JoeyStrandnes/TSTE93_Slutsteget/Documentation/Freq_Respons/html/Smooth_01.png

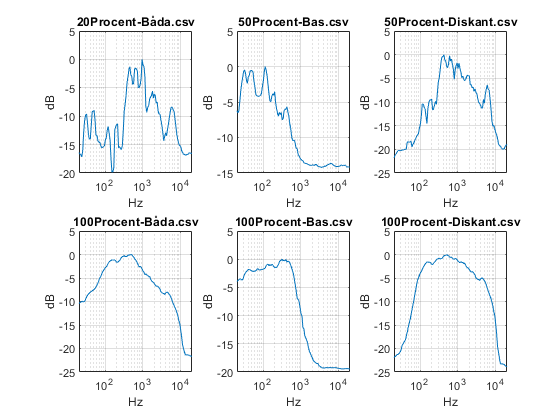
Documentation/Freq_Respons/html/Smooth_01.png
