JoeyStrandnes/TSTE93_Slutsteget/Documentation/Freq_Respons/html/Smooth_02.png

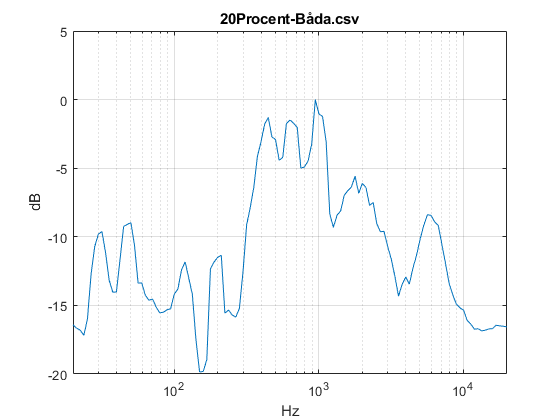
Documentation/Freq_Respons/html/Smooth_02.png
