JoeyStrandnes/TSTE93_Slutsteget/Documentation/Freq_Respons/html/Smooth_03.png

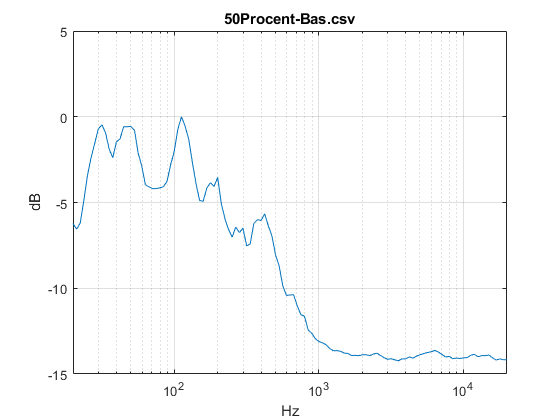
Documentation/Freq_Respons/html/Smooth_03.png
