JoeyStrandnes/TSTE93_Slutsteget/Documentation/Freq_Respons/html/Smooth_04.png

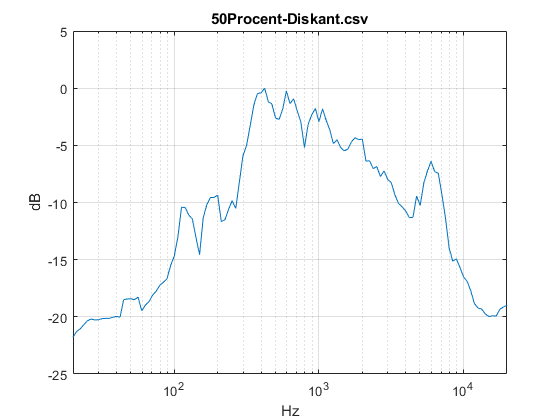
Documentation/Freq_Respons/html/Smooth_04.png
