JoeyStrandnes/TSTE93_Slutsteget/Documentation/Freq_Respons/html/Smooth_05.png

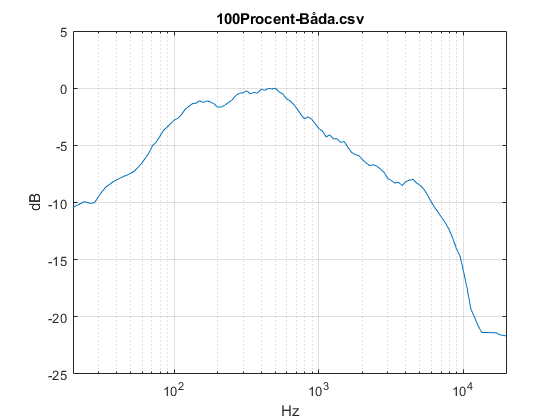
Documentation/Freq_Respons/html/Smooth_05.png
