JoeyStrandnes/TSTE93_Slutsteget/Documentation/Freq_Respons/html/Smooth_06.png

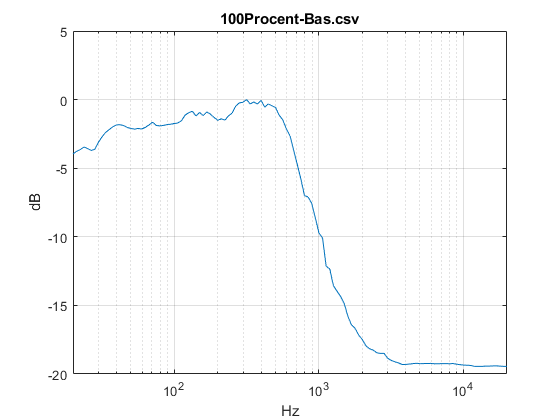
Documentation/Freq_Respons/html/Smooth_06.png
