JoeyStrandnes/TSTE93_Slutsteget/Documentation/Freq_Respons/html/Smooth_07.png

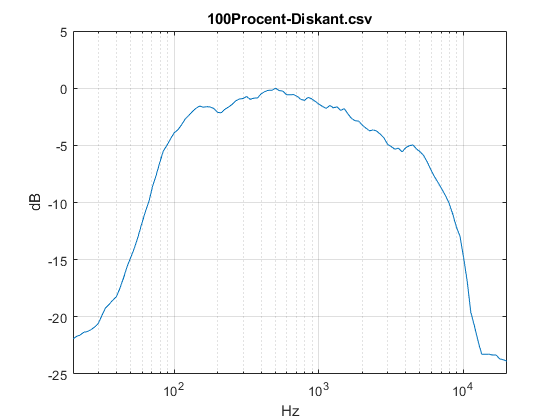
Documentation/Freq_Respons/html/Smooth_07.png
