JoeyStrandnes/TSTE93_Slutsteget/Documentation/Images/DAC-Output.png

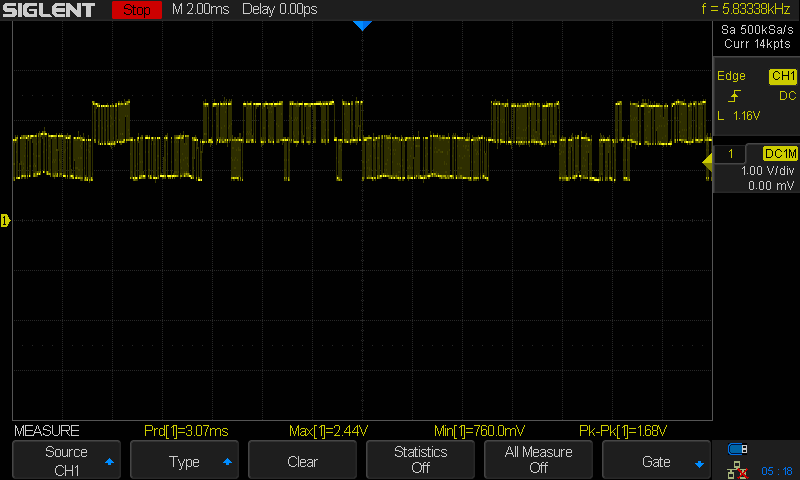
Documentation/Images/DAC-Output.png
