JoeyStrandnes/TSTE93_Slutsteget/Documentation/Images/Misc/20210310_001052.jpg

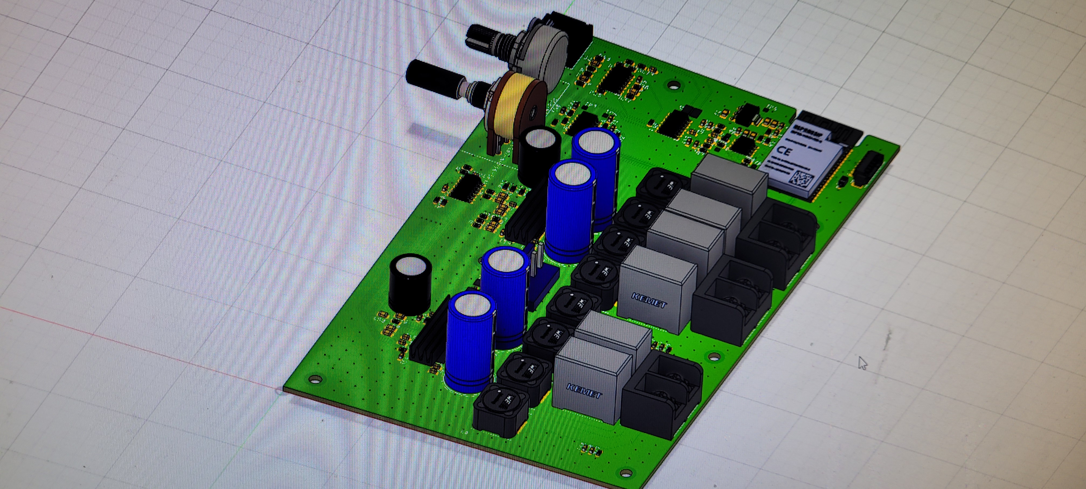
Documentation/Images/Misc/20210310_001052.jpg
