JoeyStrandnes/TSTE93_Slutsteget/Documentation/Images/Misc/20210327_163234.jpg

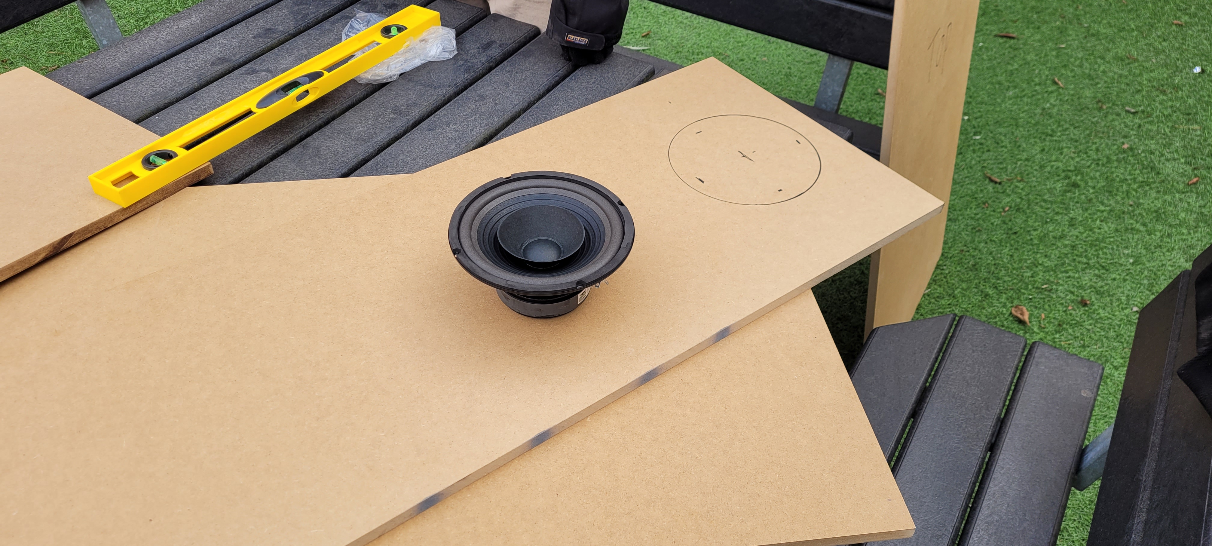
Documentation/Images/Misc/20210327_163234.jpg
