JoeyStrandnes/TSTE93_Slutsteget/Documentation/Images/Misc/20210327_163858.jpg

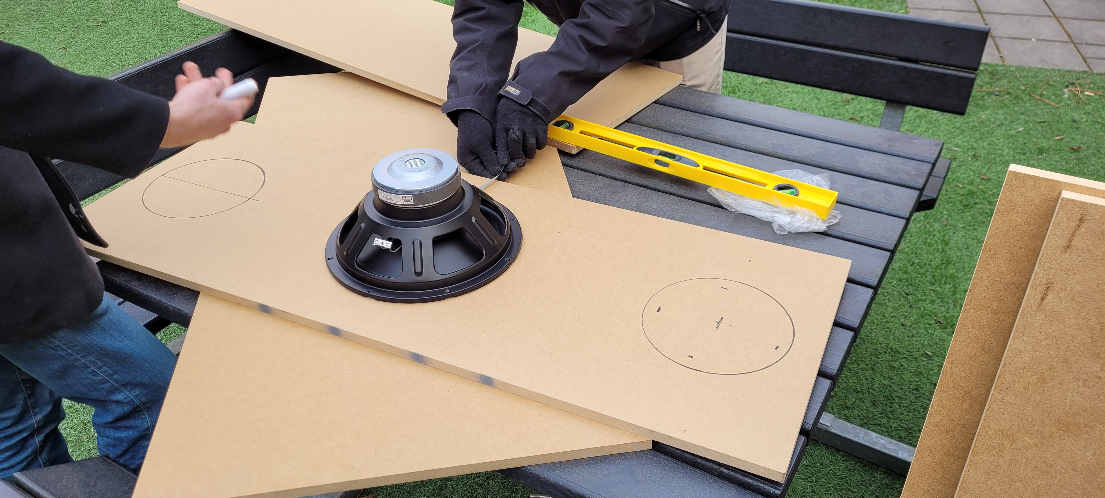
Documentation/Images/Misc/20210327_163858.jpg
