JoeyStrandnes/TSTE93_Slutsteget/Documentation/Images/Misc/20210327_181533.jpg

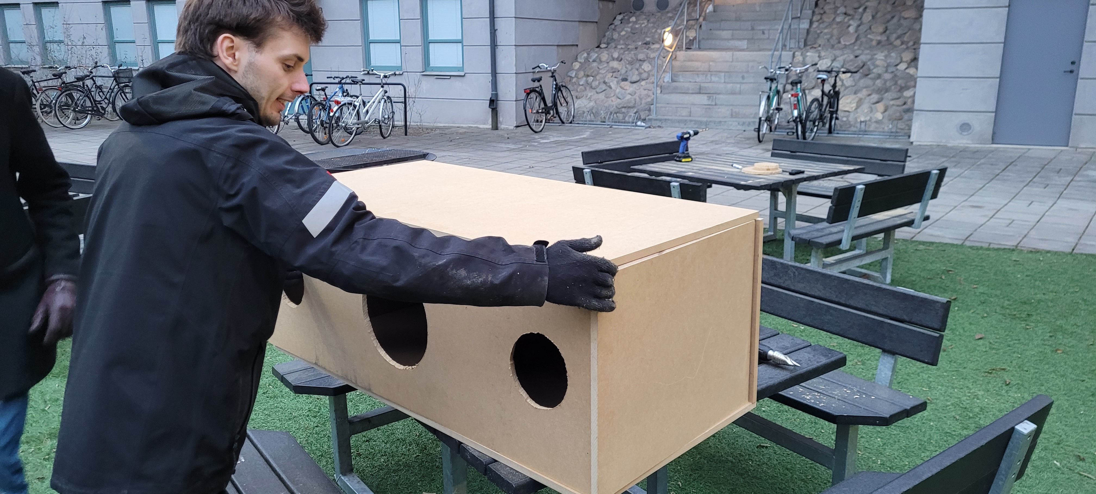
Documentation/Images/Misc/20210327_181533.jpg
