JoeyStrandnes/TSTE93_Slutsteget/Documentation/Images/Misc/20210327_181544.jpg

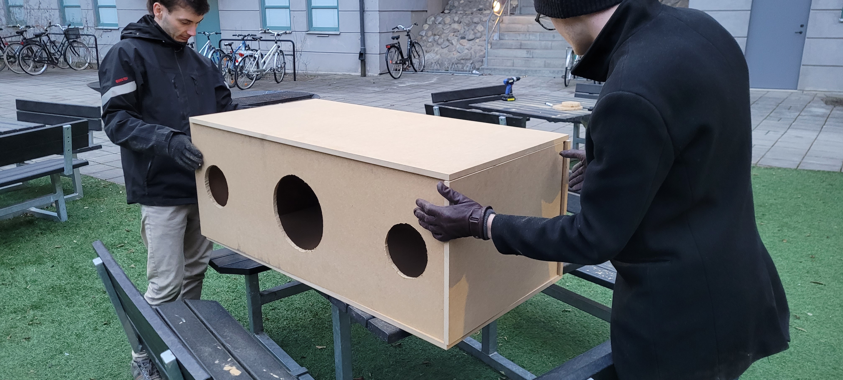
Documentation/Images/Misc/20210327_181544.jpg
