JoeyStrandnes/TSTE93_Slutsteget/Documentation/Images/Misc/20210410_160741.jpg

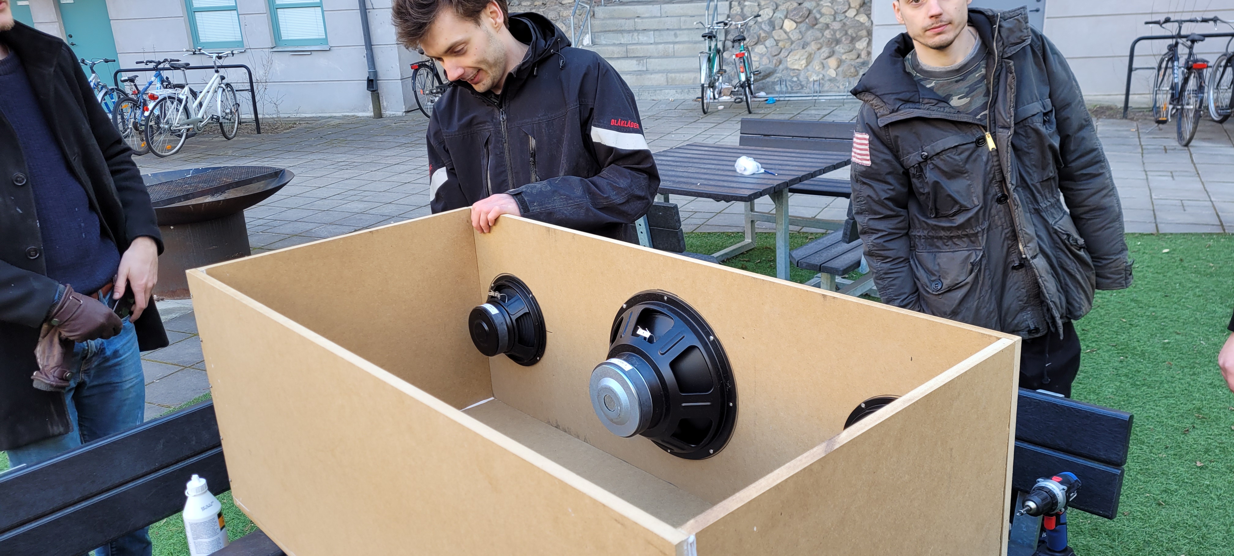
Documentation/Images/Misc/20210410_160741.jpg
