JoeyStrandnes/TSTE93_Slutsteget/Documentation/Images/Misc/20210410_160745.jpg

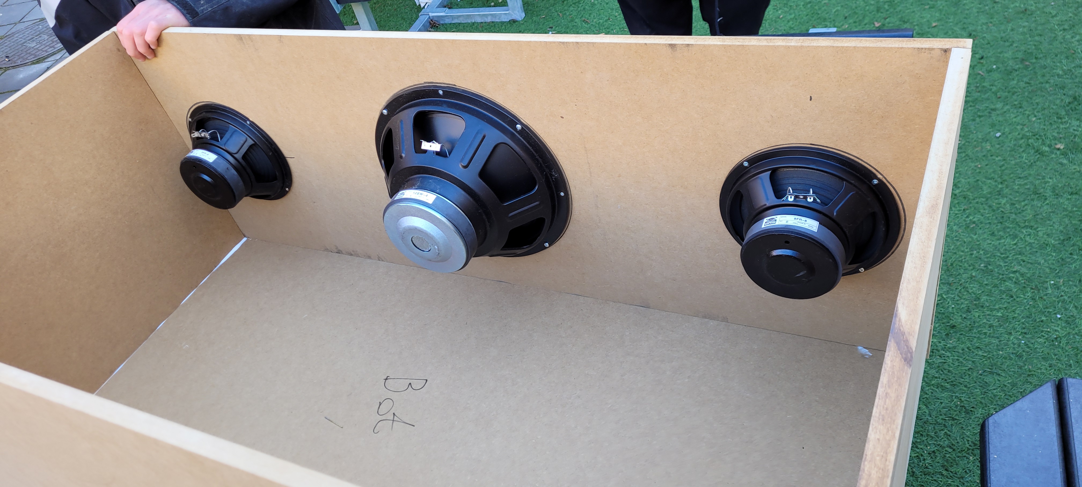
Documentation/Images/Misc/20210410_160745.jpg
