JoeyStrandnes/TSTE93_Slutsteget/Documentation/Images/Misc/20210410_163332.jpg

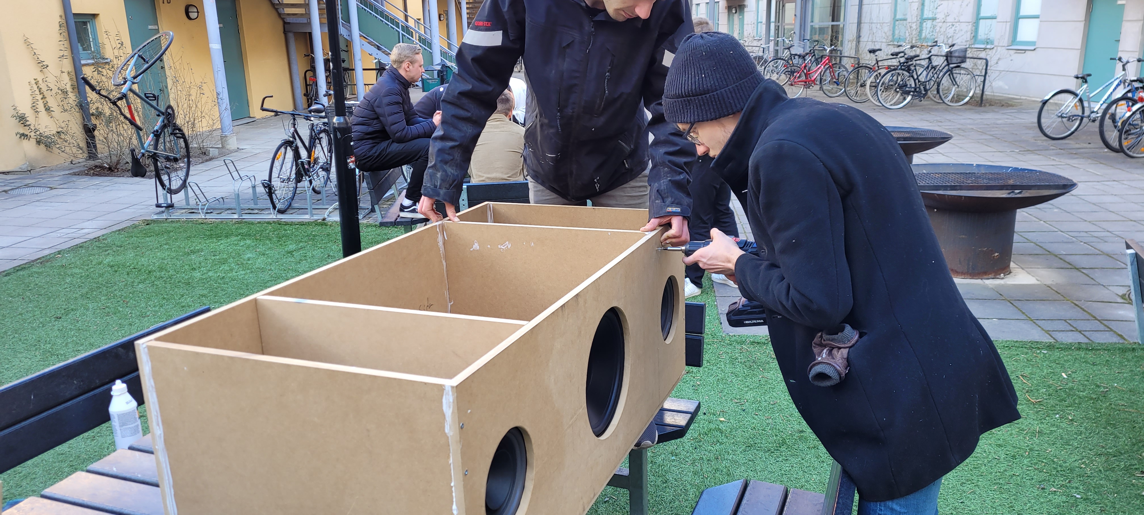
Documentation/Images/Misc/20210410_163332.jpg
