JoeyStrandnes/TSTE93_Slutsteget/Documentation/Images/Misc/20210410_163335.jpg

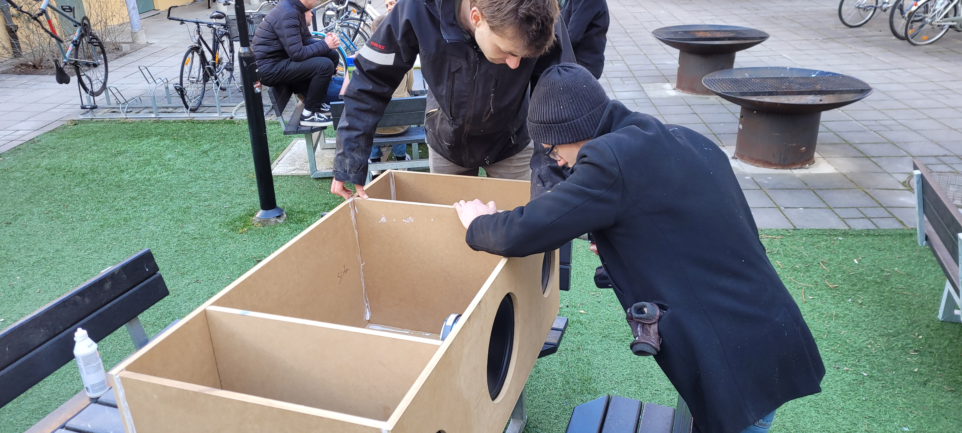
Documentation/Images/Misc/20210410_163335.jpg
