JoeyStrandnes/TSTE93_Slutsteget/Documentation/Images/Misc/20210410_163340.jpg

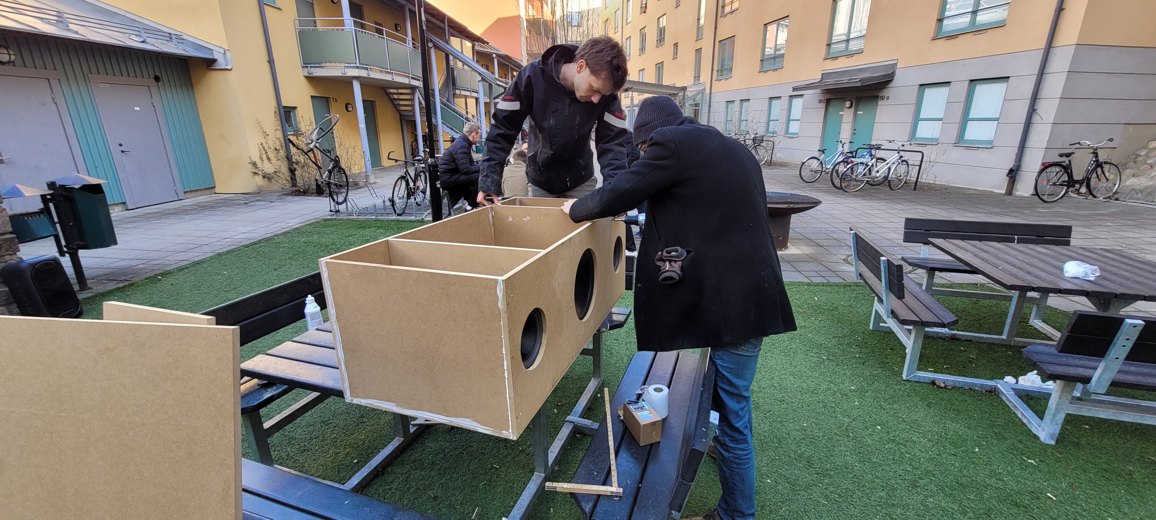
Documentation/Images/Misc/20210410_163340.jpg
