JoeyStrandnes/TSTE93_Slutsteget/Documentation/Images/Misc/20210410_170837.jpg

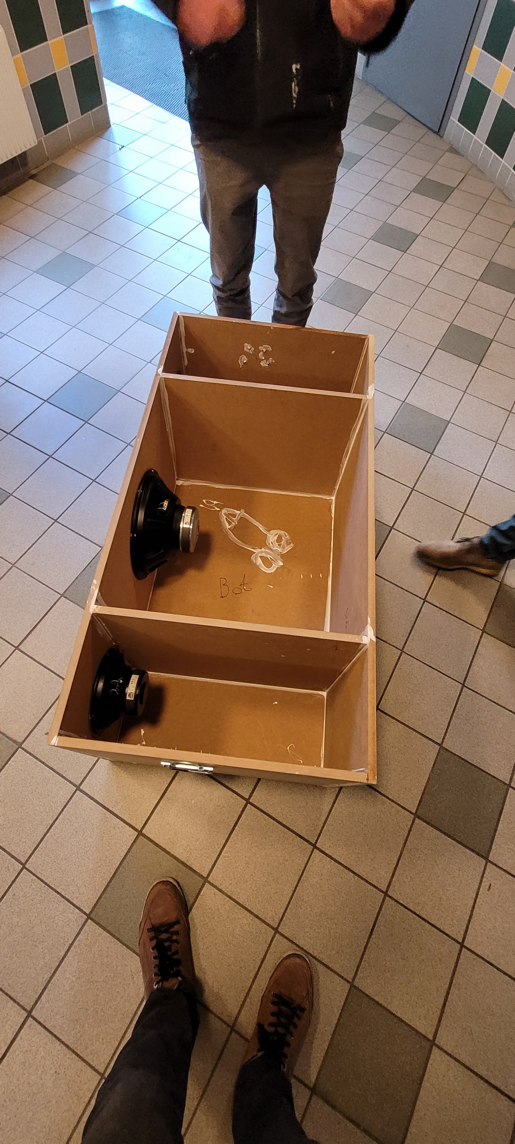
Documentation/Images/Misc/20210410_170837.jpg
