JoeyStrandnes/TSTE93_Slutsteget/Documentation/Images/Misc/20210410_170842.jpg

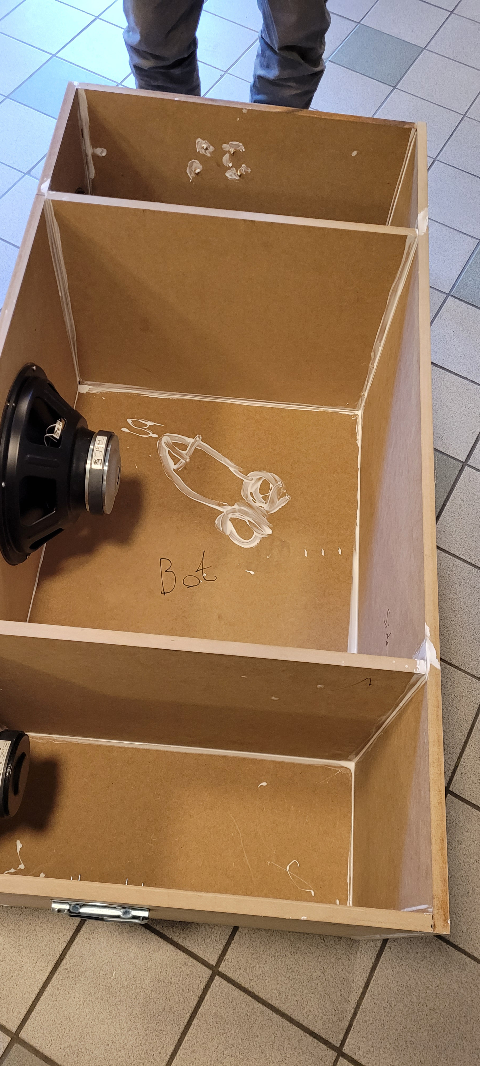
Documentation/Images/Misc/20210410_170842.jpg
