JoeyStrandnes/TSTE93_Slutsteget/Documentation/Images/Misc/20210417_114759.jpg

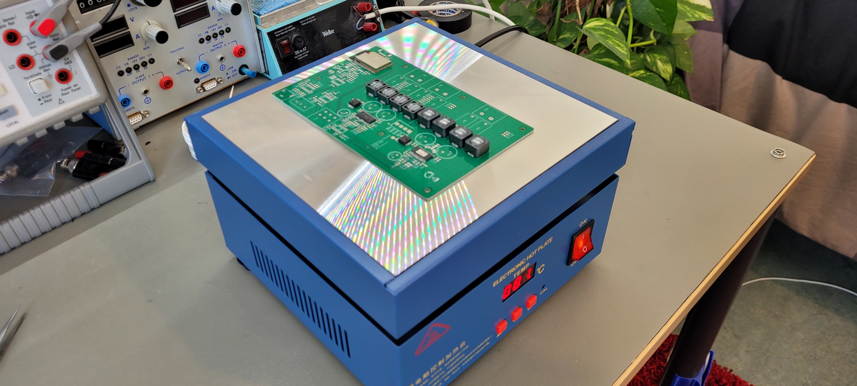
Documentation/Images/Misc/20210417_114759.jpg
