JoeyStrandnes/TSTE93_Slutsteget/Documentation/Images/Misc/20210417_114805.jpg

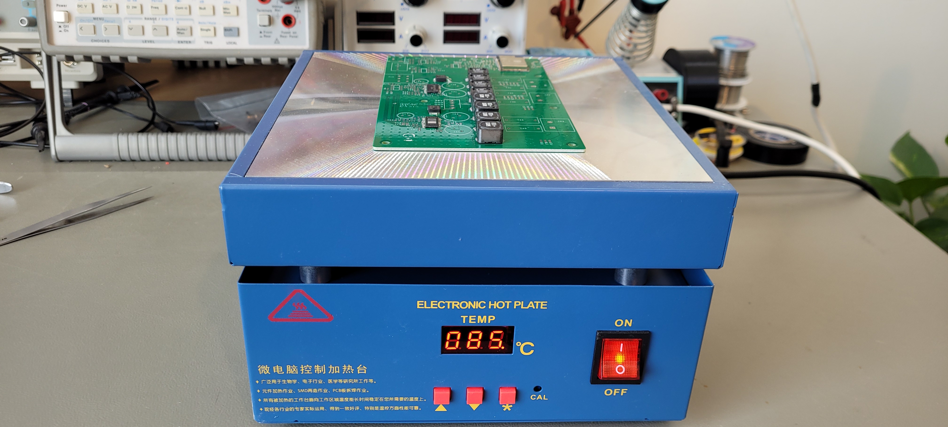
Documentation/Images/Misc/20210417_114805.jpg
