JoeyStrandnes/TSTE93_Slutsteget/Documentation/Images/Misc/20210417_114810.jpg

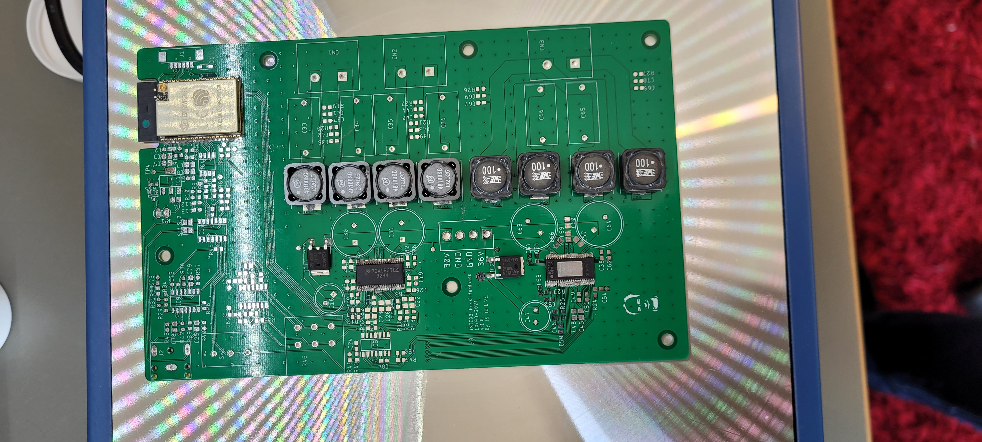
Documentation/Images/Misc/20210417_114810.jpg
