JoeyStrandnes/TSTE93_Slutsteget/Documentation/Images/Misc/20210417_114818.jpg

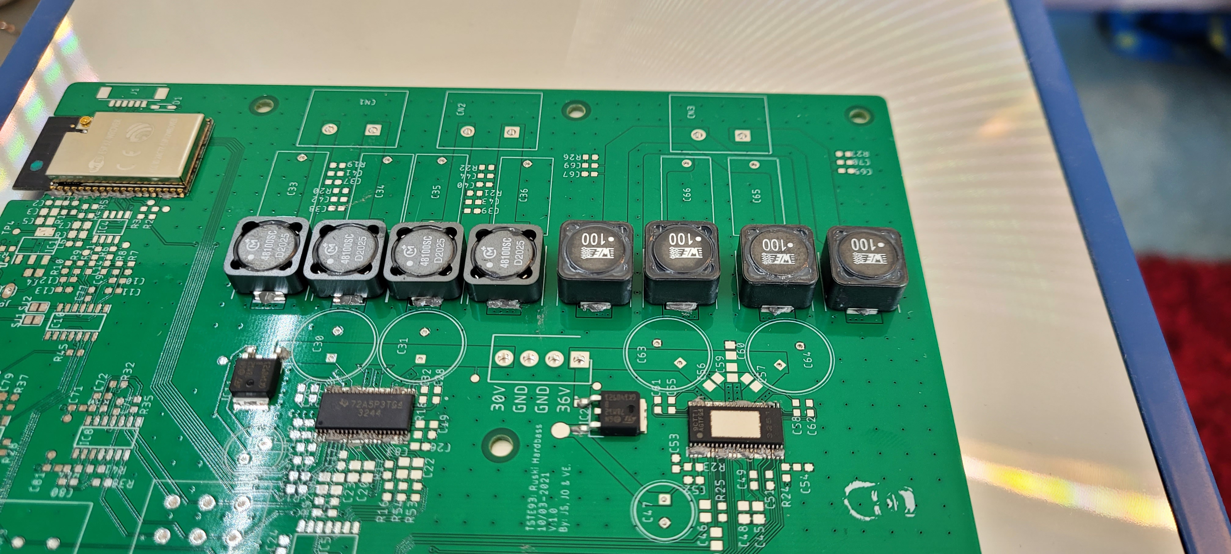
Documentation/Images/Misc/20210417_114818.jpg
