JoeyStrandnes/TSTE93_Slutsteget/Documentation/Images/Misc/20210417_170538.jpg

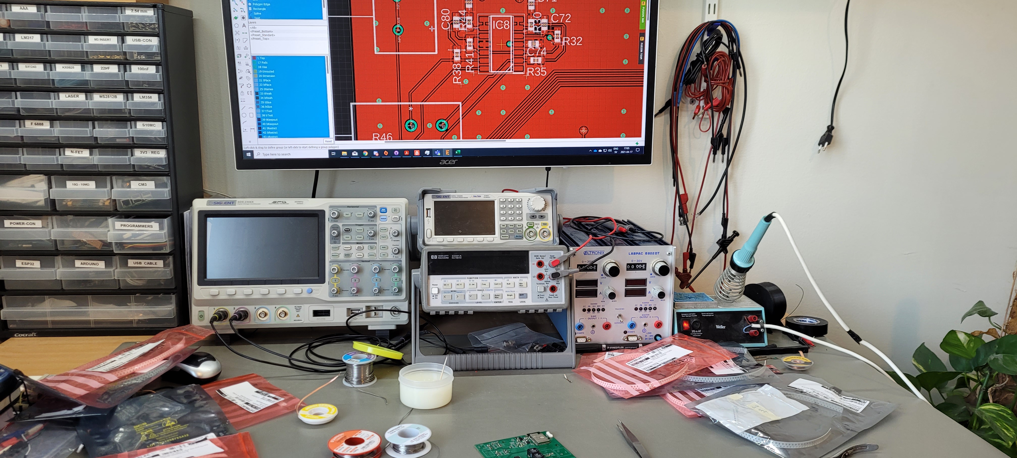
Documentation/Images/Misc/20210417_170538.jpg
