JoeyStrandnes/TSTE93_Slutsteget/Documentation/Images/Misc/20210417_171242.jpg

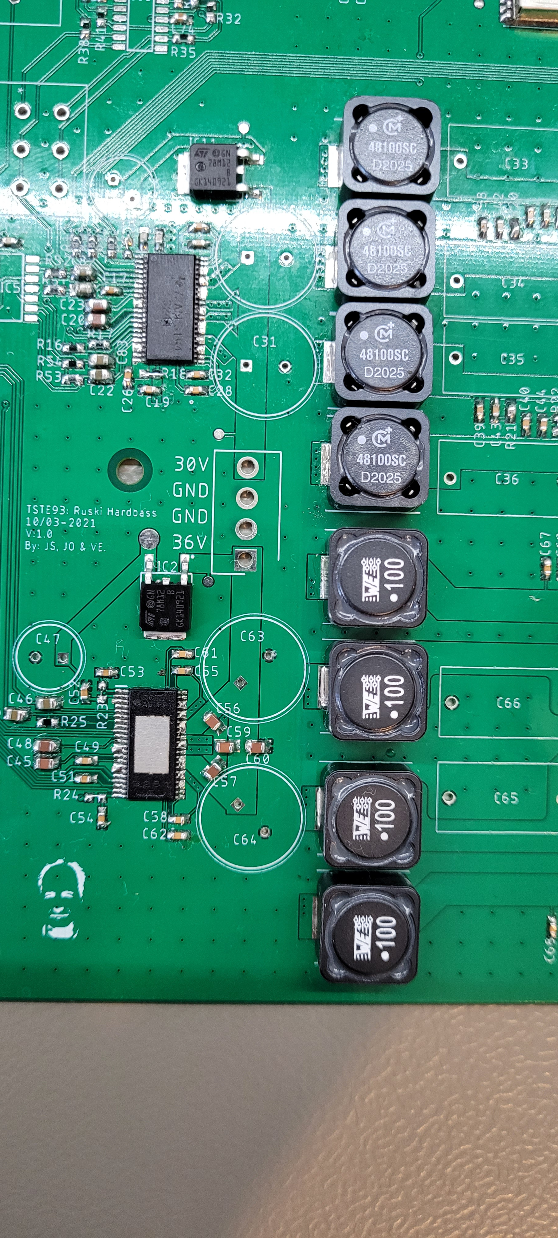
Documentation/Images/Misc/20210417_171242.jpg
