JoeyStrandnes/TSTE93_Slutsteget/Documentation/Images/Misc/20210417_171250.jpg

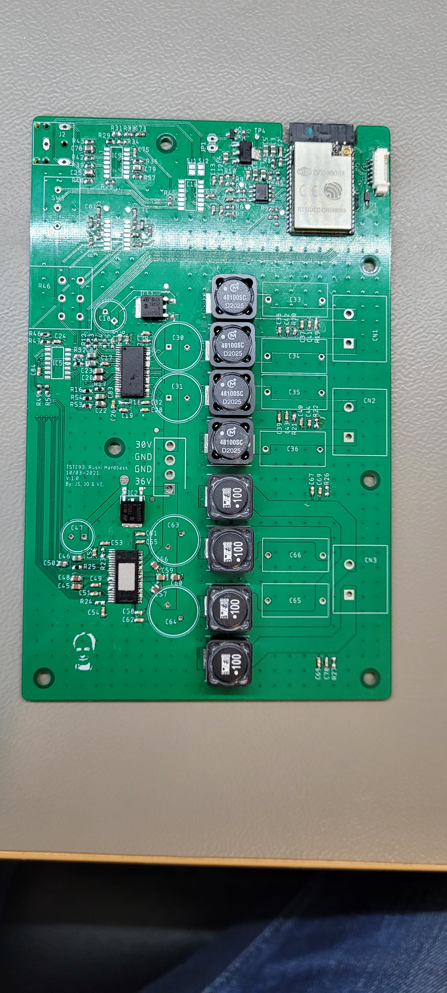
Documentation/Images/Misc/20210417_171250.jpg
