JoeyStrandnes/TSTE93_Slutsteget/Documentation/Images/Misc/20210417_171255.jpg

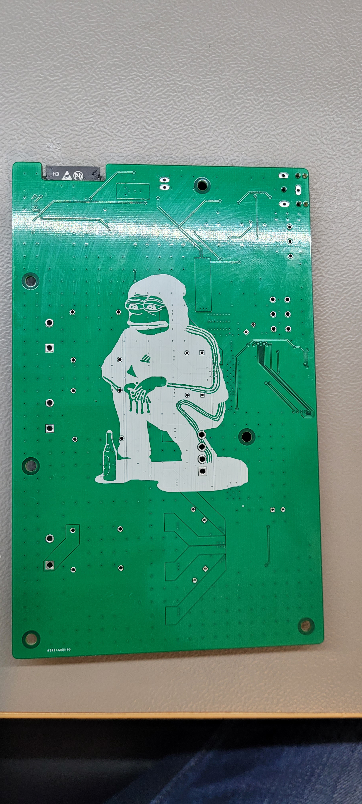
Documentation/Images/Misc/20210417_171255.jpg
