JoeyStrandnes/TSTE93_Slutsteget/Documentation/Images/Misc/20210417_173522.jpg

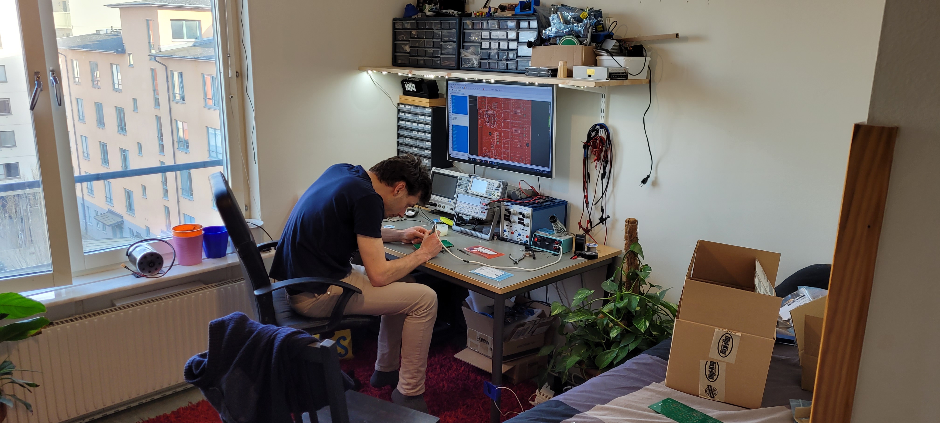
Documentation/Images/Misc/20210417_173522.jpg
