JoeyStrandnes/TSTE93_Slutsteget/Documentation/Images/Misc/20210417_173532.jpg

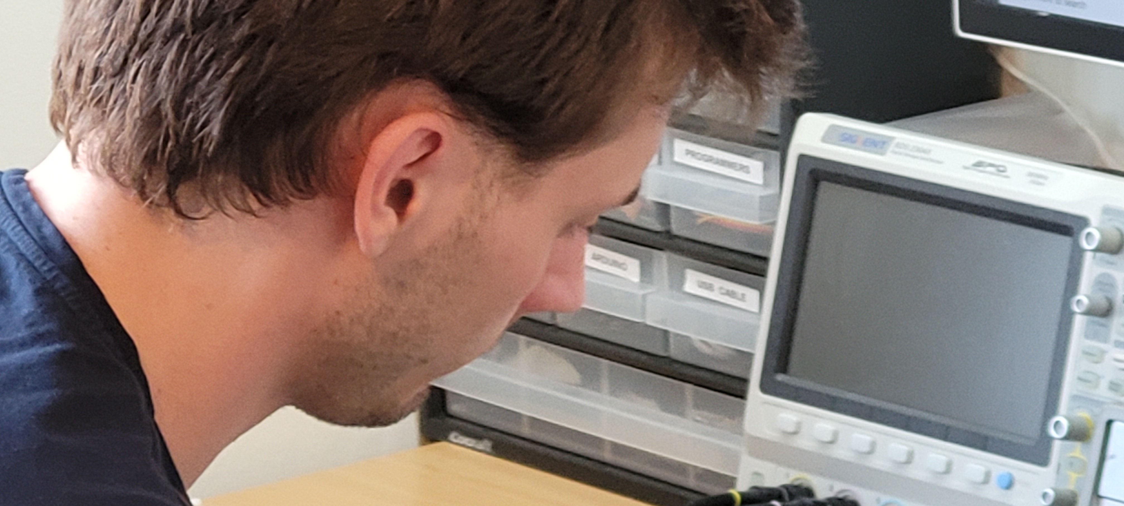
Documentation/Images/Misc/20210417_173532.jpg
