JoeyStrandnes/TSTE93_Slutsteget/Documentation/Images/Misc/20210417_185742.jpg

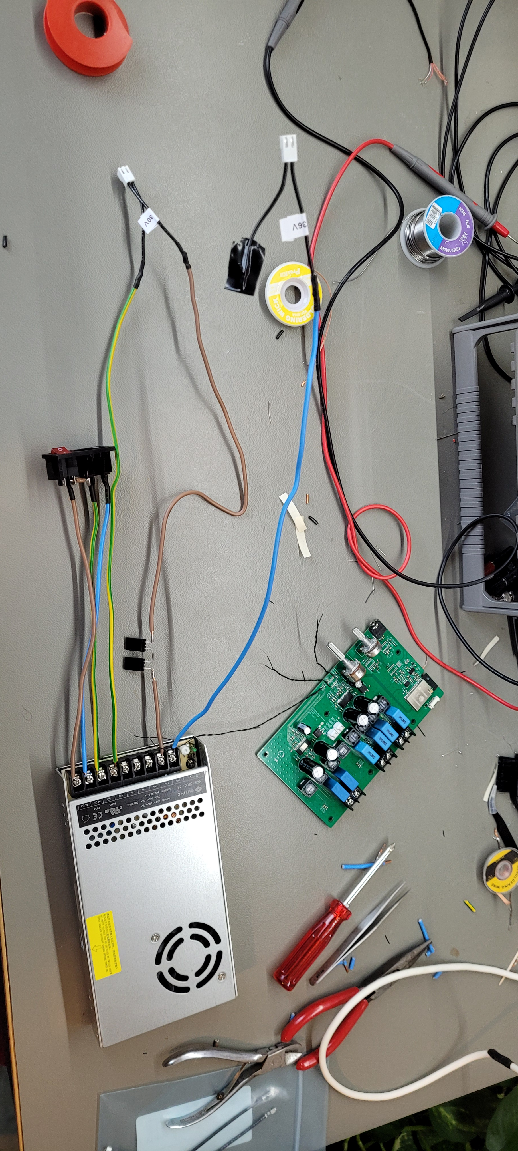
Documentation/Images/Misc/20210417_185742.jpg
