JoeyStrandnes/TSTE93_Slutsteget/Documentation/Images/Misc/20210417_185746.jpg

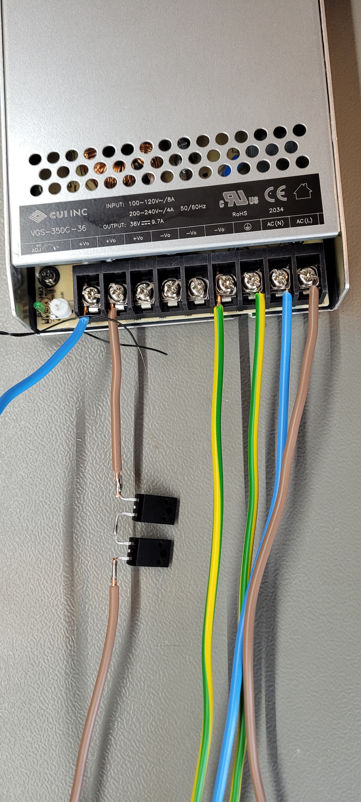
Documentation/Images/Misc/20210417_185746.jpg
