JoeyStrandnes/TSTE93_Slutsteget/Documentation/Images/Misc/20210417_185757.jpg

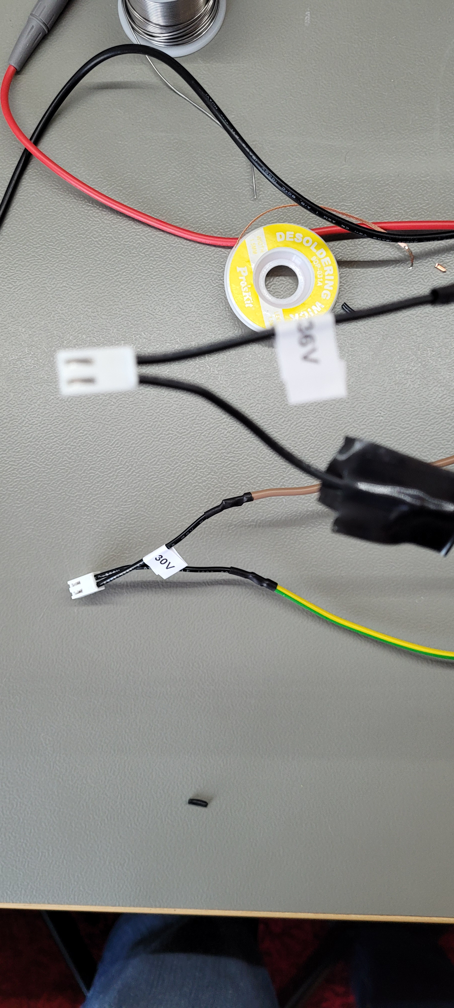
Documentation/Images/Misc/20210417_185757.jpg
