JoeyStrandnes/TSTE93_Slutsteget/Documentation/Images/Misc/20210417_190529.jpg

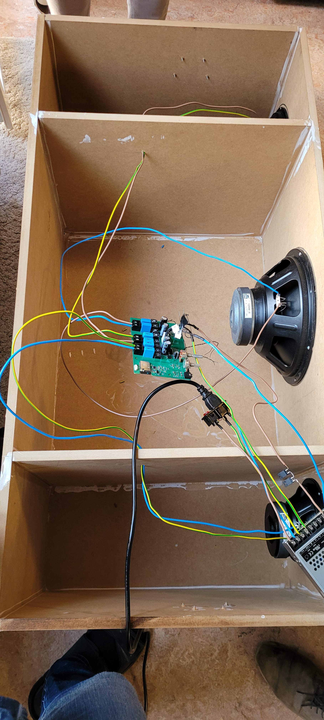
Documentation/Images/Misc/20210417_190529.jpg
