JoeyStrandnes/TSTE93_Slutsteget/Documentation/Images/Misc/20210417_190536.jpg

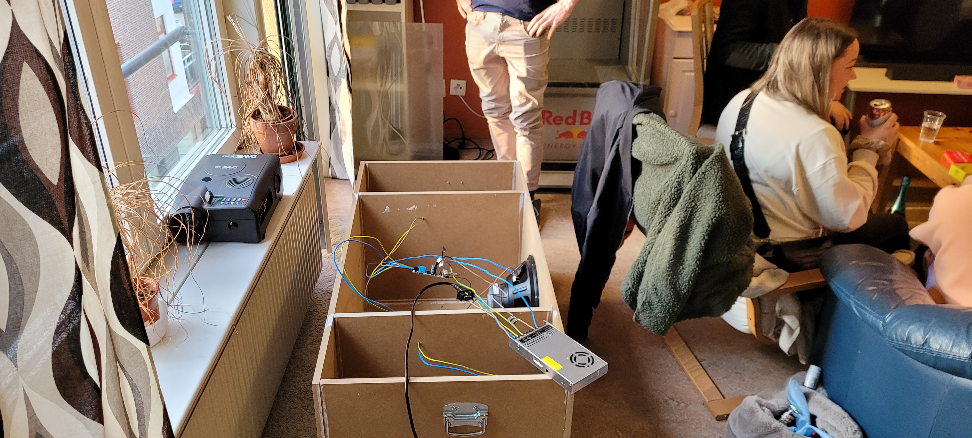
Documentation/Images/Misc/20210417_190536.jpg
