JoeyStrandnes/TSTE93_Slutsteget/Documentation/Images/Misc/20210430_175258.jpg

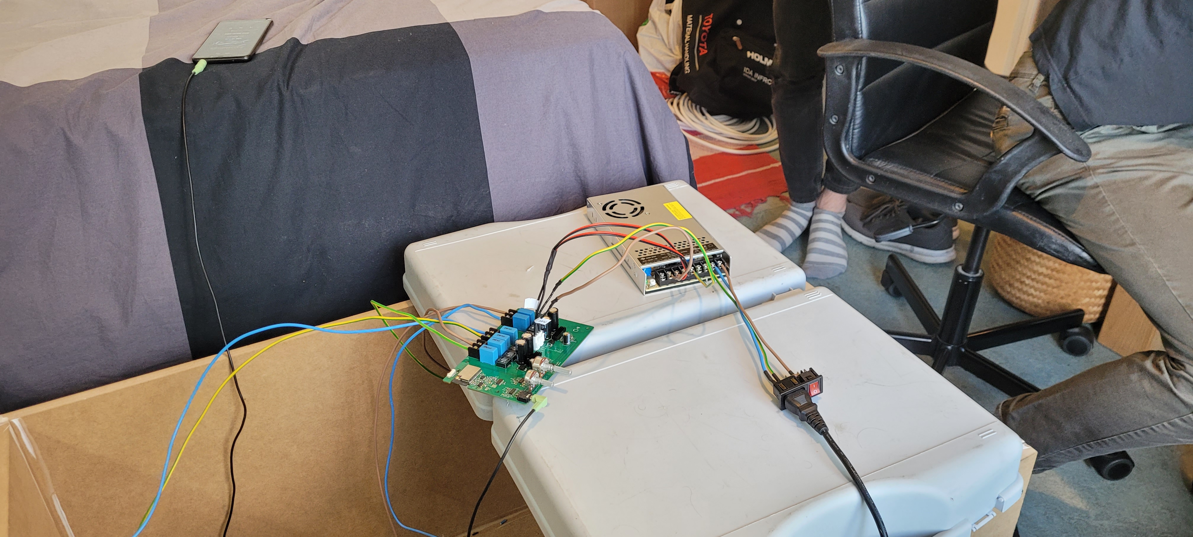
Documentation/Images/Misc/20210430_175258.jpg
