JoeyStrandnes/TSTE93_Slutsteget/Documentation/Images/Misc/20210430_175302.jpg

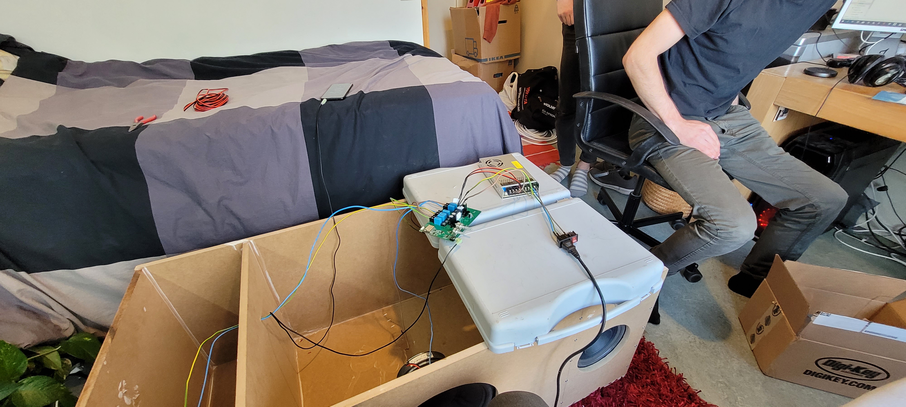
Documentation/Images/Misc/20210430_175302.jpg
