JoeyStrandnes/TSTE93_Slutsteget/Documentation/Images/Misc/20210430_175306.jpg

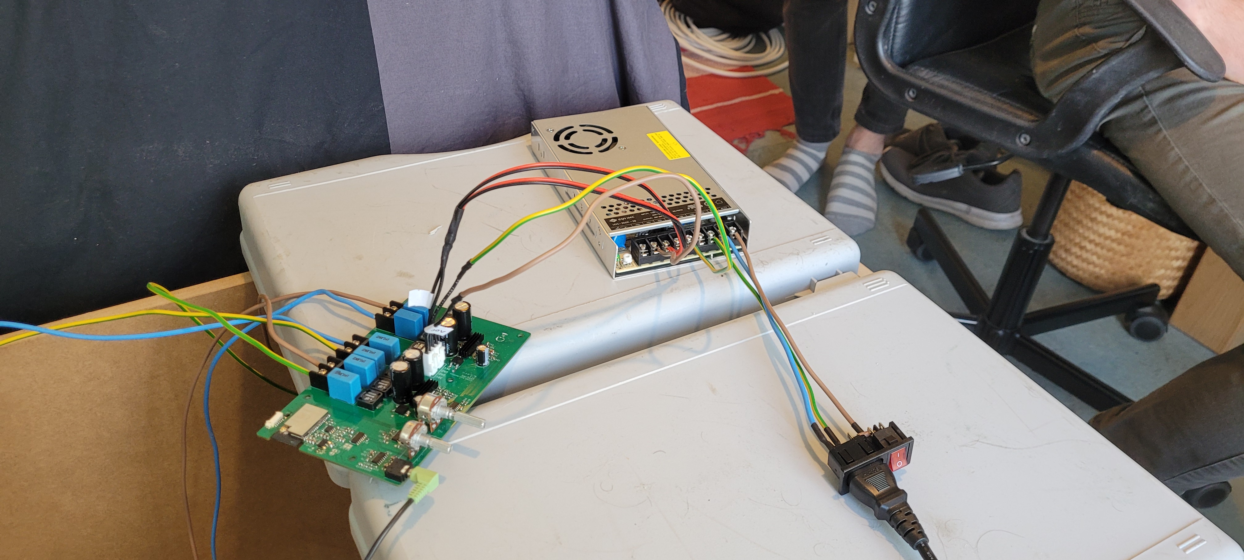
Documentation/Images/Misc/20210430_175306.jpg
