JoeyStrandnes/TSTE93_Slutsteget/Documentation/Images/Misc/20210501_010639.jpg

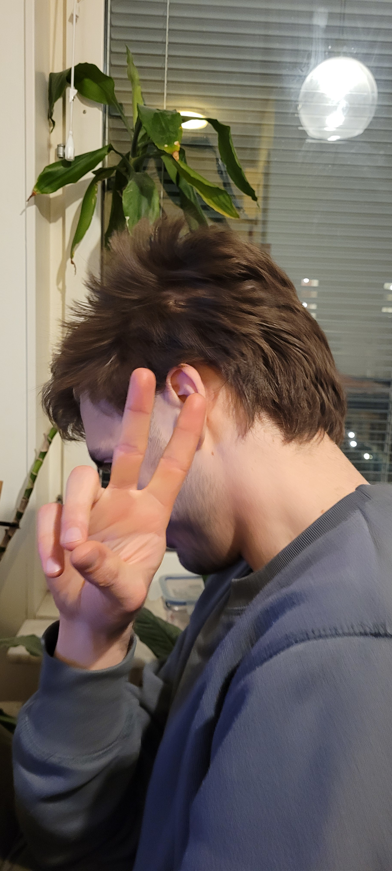
Documentation/Images/Misc/20210501_010639.jpg
