JoeyStrandnes/TSTE93_Slutsteget/Documentation/Images/Misc/20210508_111350.jpg

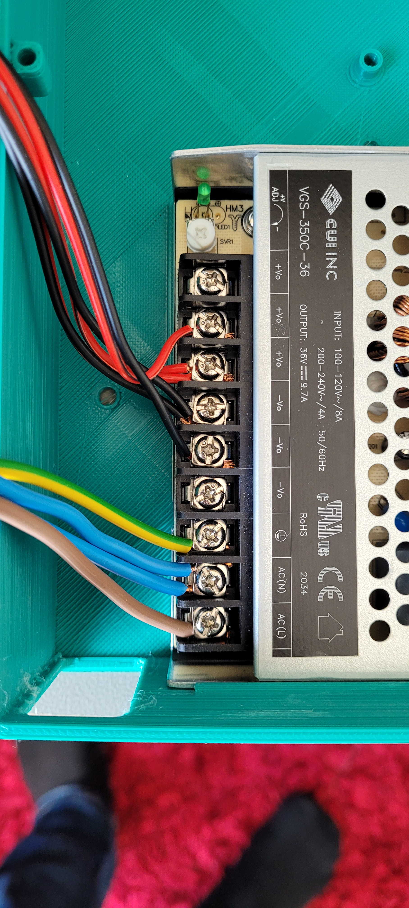
Documentation/Images/Misc/20210508_111350.jpg
