JoeyStrandnes/TSTE93_Slutsteget/Documentation/Images/Misc/20210508_113425.jpg

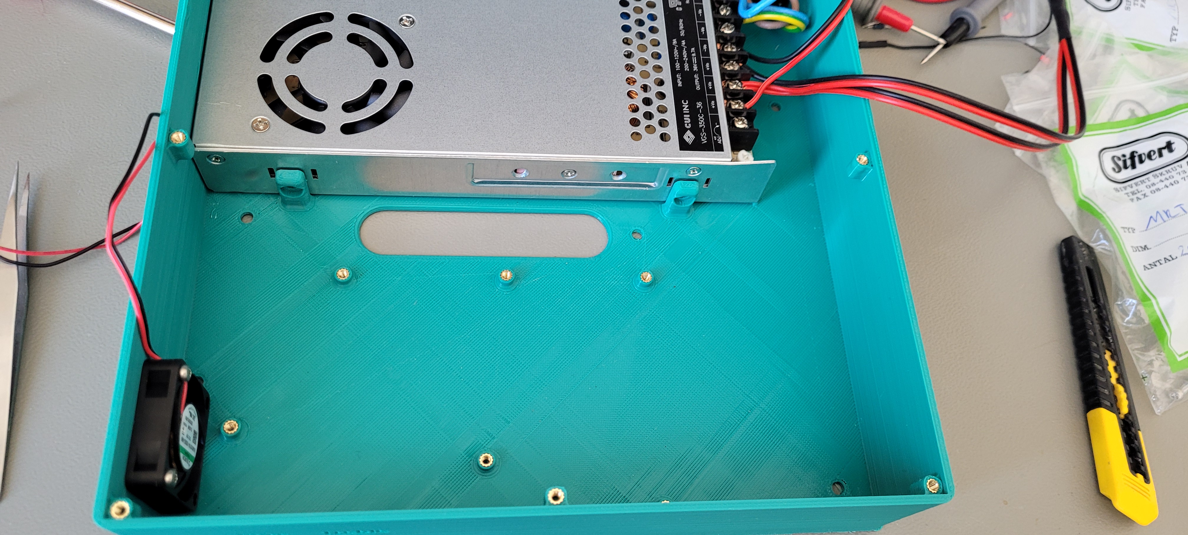
Documentation/Images/Misc/20210508_113425.jpg
