JoeyStrandnes/TSTE93_Slutsteget/Documentation/Images/Misc/20210508_113429.jpg

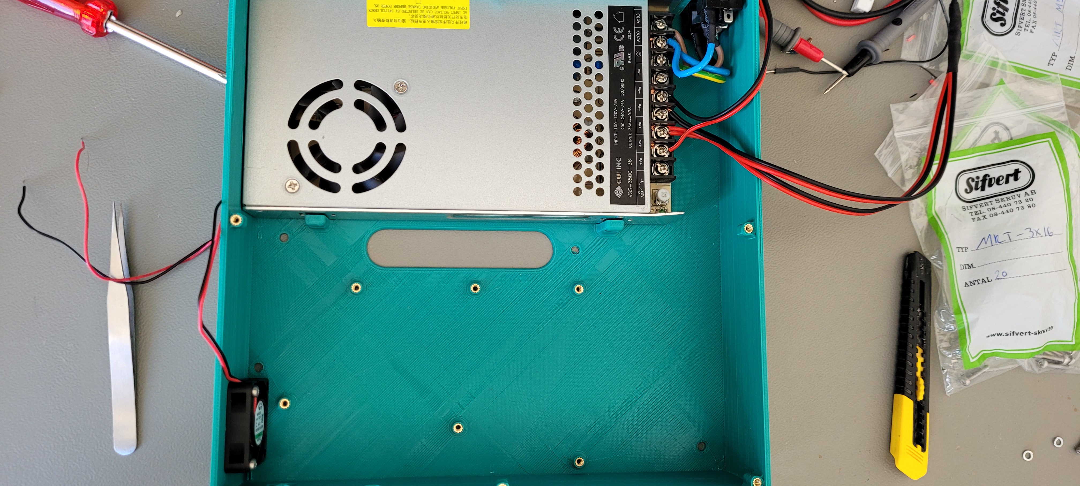
Documentation/Images/Misc/20210508_113429.jpg
