JoeyStrandnes/TSTE93_Slutsteget/Documentation/Images/Misc/20210508_114451.jpg

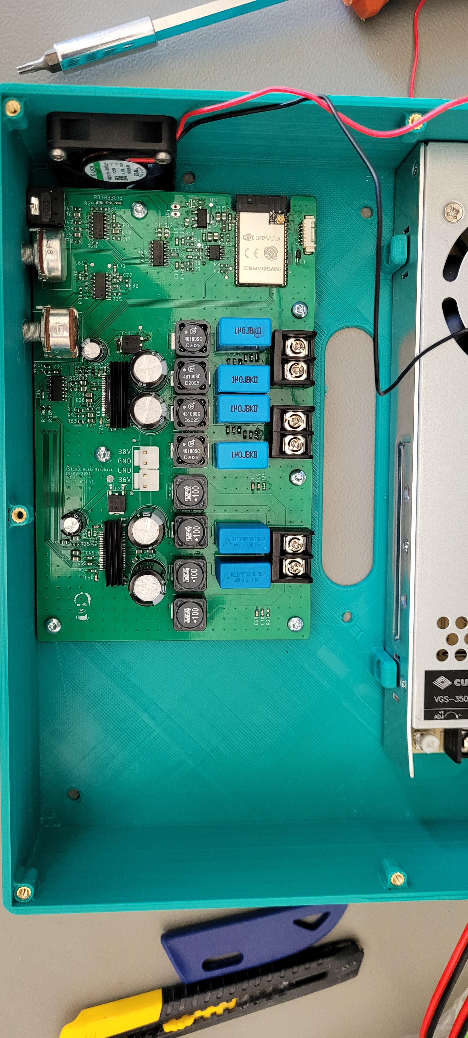
Documentation/Images/Misc/20210508_114451.jpg
