JoeyStrandnes/TSTE93_Slutsteget/Documentation/Images/Misc/20210508_114456.jpg

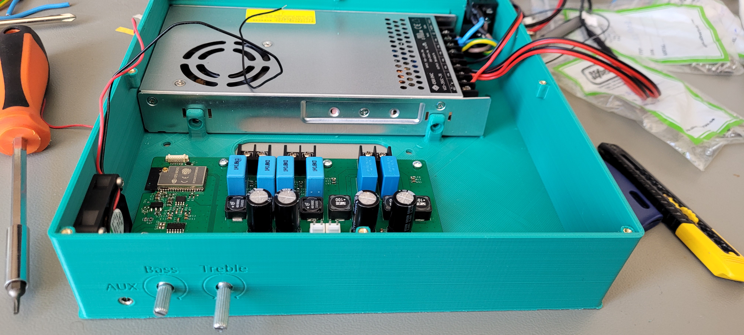
Documentation/Images/Misc/20210508_114456.jpg
