JoeyStrandnes/TSTE93_Slutsteget/Documentation/Images/Misc/20210508_124219.jpg

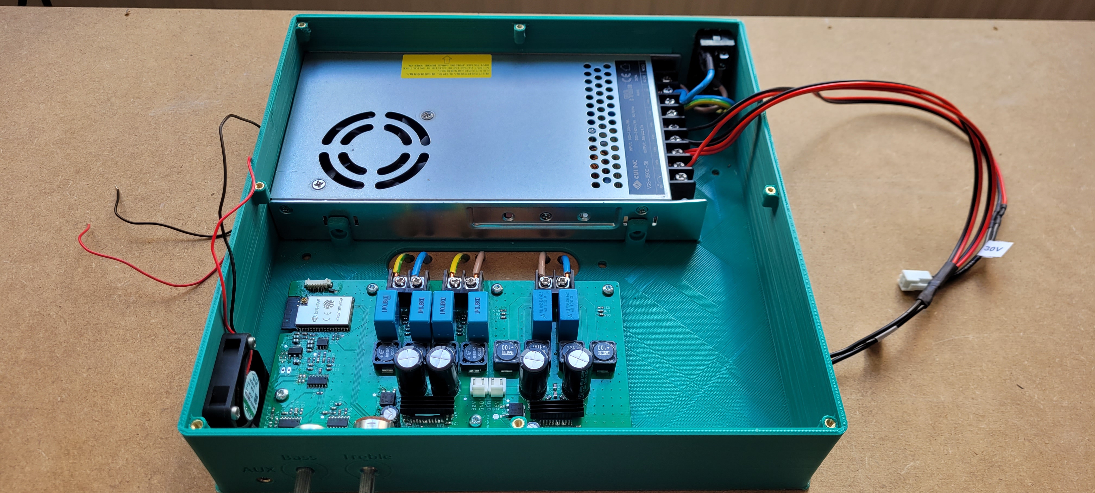
Documentation/Images/Misc/20210508_124219.jpg
