JoeyStrandnes/TSTE93_Slutsteget/Documentation/Images/Misc/20210508_171244.jpg

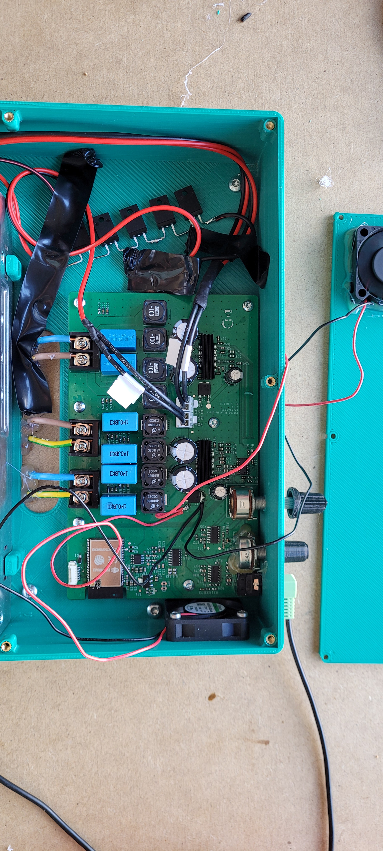
Documentation/Images/Misc/20210508_171244.jpg
