JoeyStrandnes/TSTE93_Slutsteget/Documentation/Images/Misc/20210508_182800.jpg

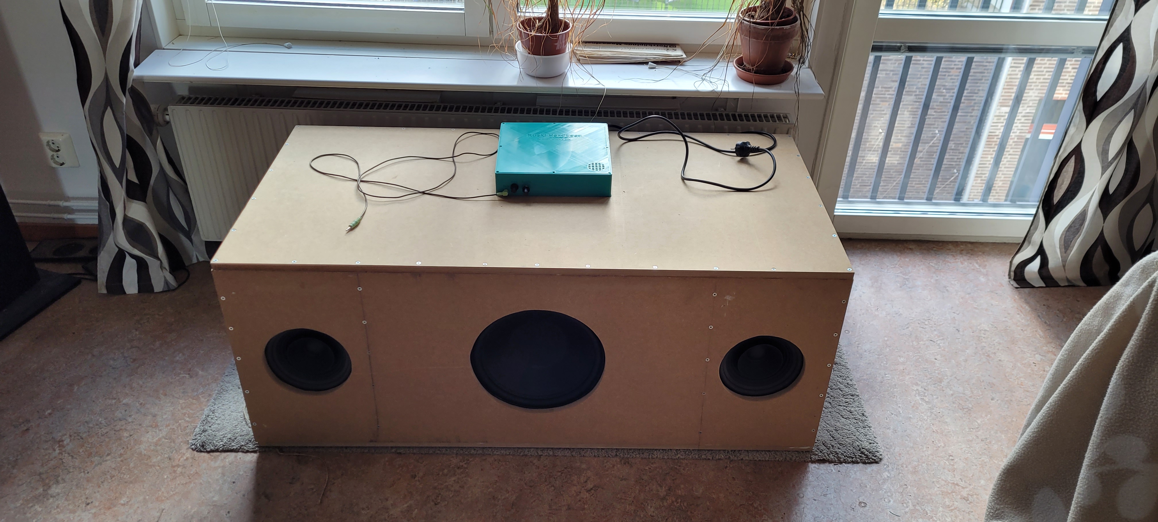
Documentation/Images/Misc/20210508_182800.jpg
