JoeyStrandnes/TSTE93_Slutsteget/Documentation/Images/Misc/20210508_182803.jpg

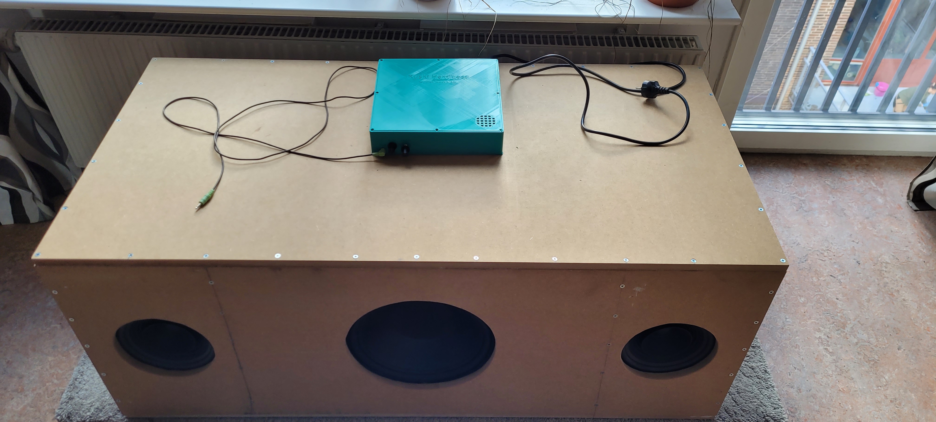
Documentation/Images/Misc/20210508_182803.jpg
