JoeyStrandnes/TSTE93_Slutsteget/Documentation/Images/Misc/20210508_182808.jpg

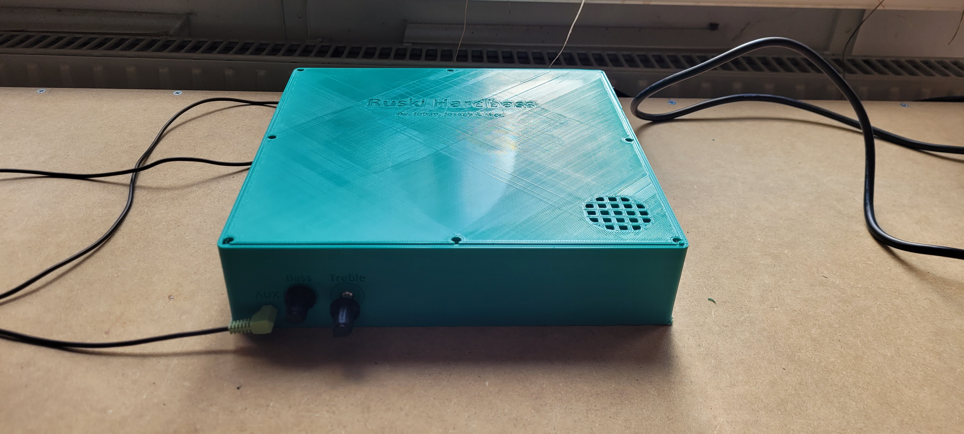
Documentation/Images/Misc/20210508_182808.jpg
