JoeyStrandnes/TSTE93_Slutsteget/Documentation/Images/Misc/20210519_163144.jpg

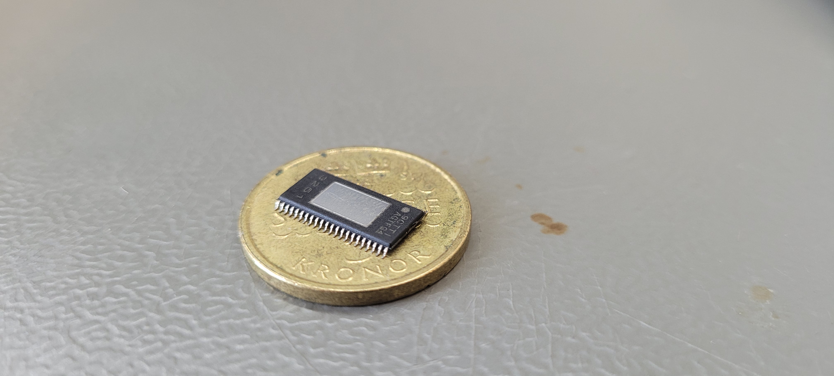
Documentation/Images/Misc/20210519_163144.jpg
