JoeyStrandnes/TSTE93_Slutsteget/Documentation/Images/Misc/20210519_163241.jpg

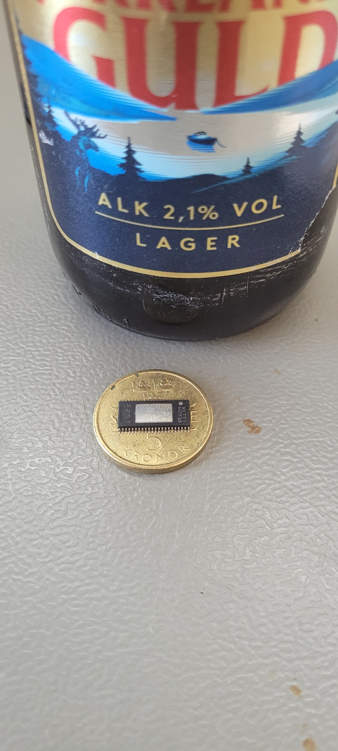
Documentation/Images/Misc/20210519_163241.jpg
