JoeyStrandnes/TSTE93_Slutsteget/Documentation/Images/Misc/20210519_163252.jpg

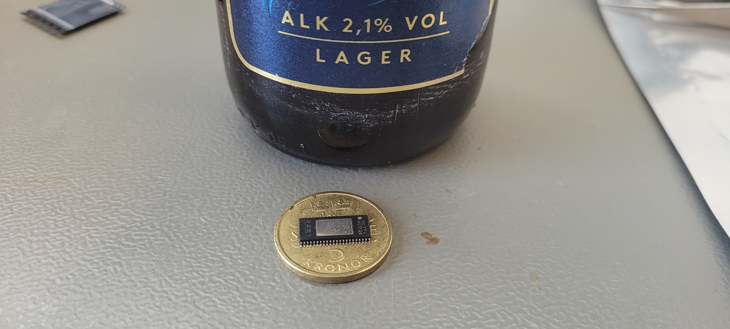
Documentation/Images/Misc/20210519_163252.jpg
