JoeyStrandnes/TSTE93_Slutsteget/Documentation/Images/Misc/Box_Above.jpg

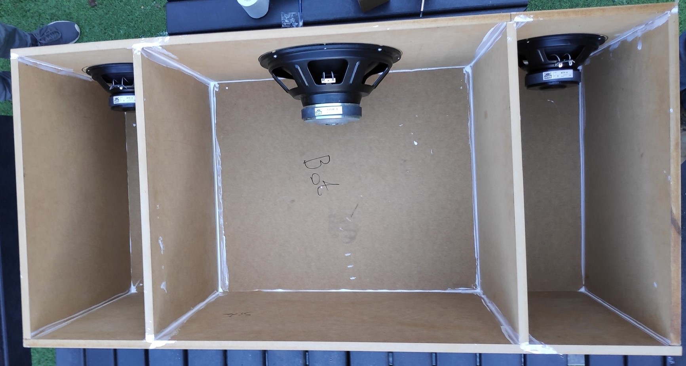
Documentation/Images/Misc/Box_Above.jpg
