JoeyStrandnes/TSTE93_Slutsteget/Documentation/Images/Multisim/MultiSim_AC_Both.png

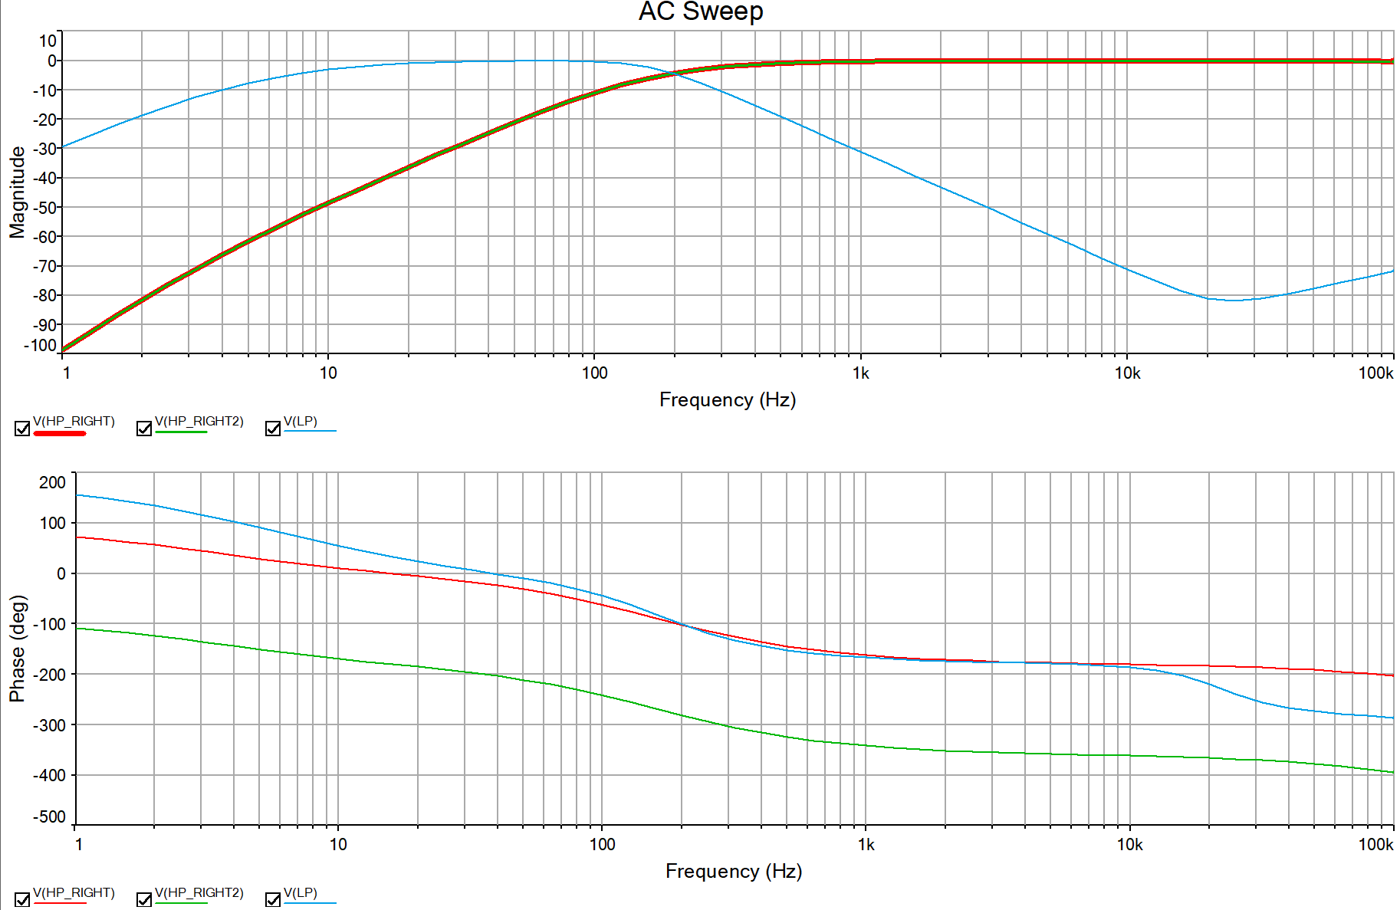
Documentation/Images/Multisim/MultiSim_AC_Both.png
