JoeyStrandnes/TSTE93_Slutsteget/Documentation/Images/Multisim/MultiSim_AC_sweep.png

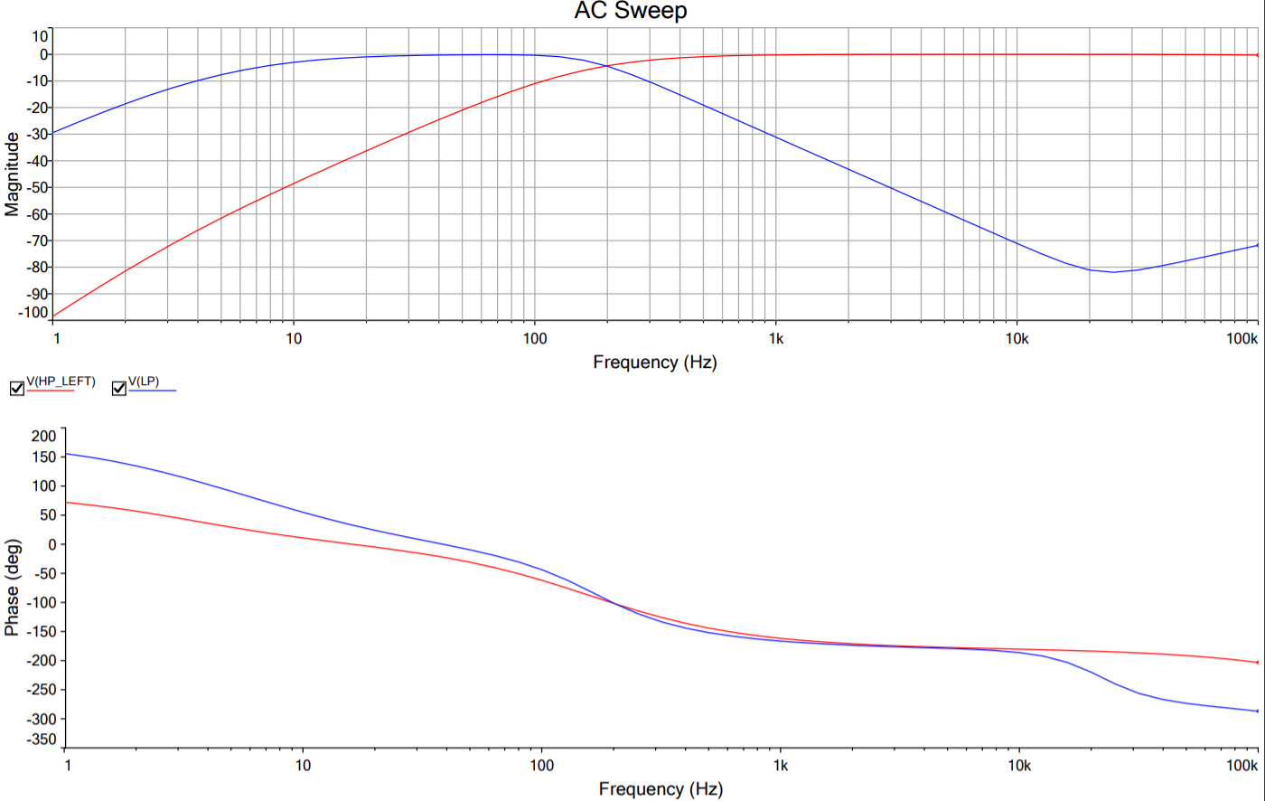
Documentation/Images/Multisim/MultiSim_AC_sweep.png
