JoeyStrandnes/TSTE93_Slutsteget/Documentation/Images/Multisim/MultiSim_HP.png

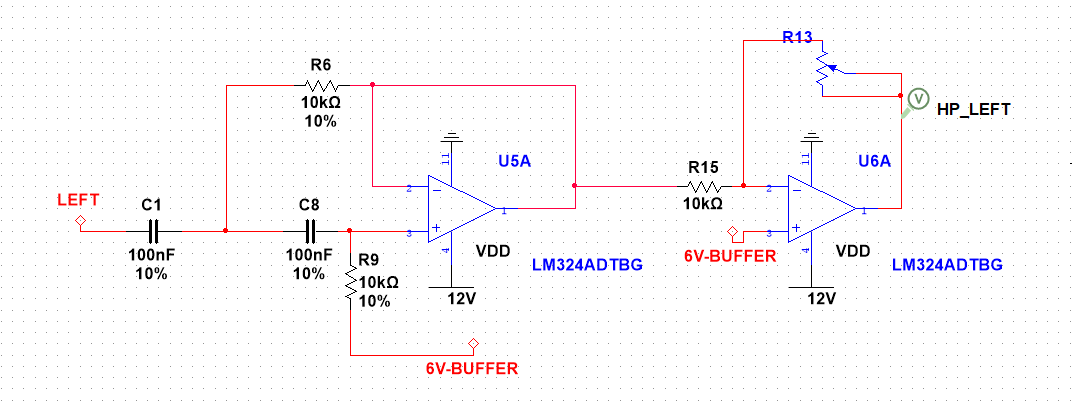
Documentation/Images/Multisim/MultiSim_HP.png
