JoeyStrandnes/TSTE93_Slutsteget/Documentation/Images/Multisim/MultiSim_HP_2.png

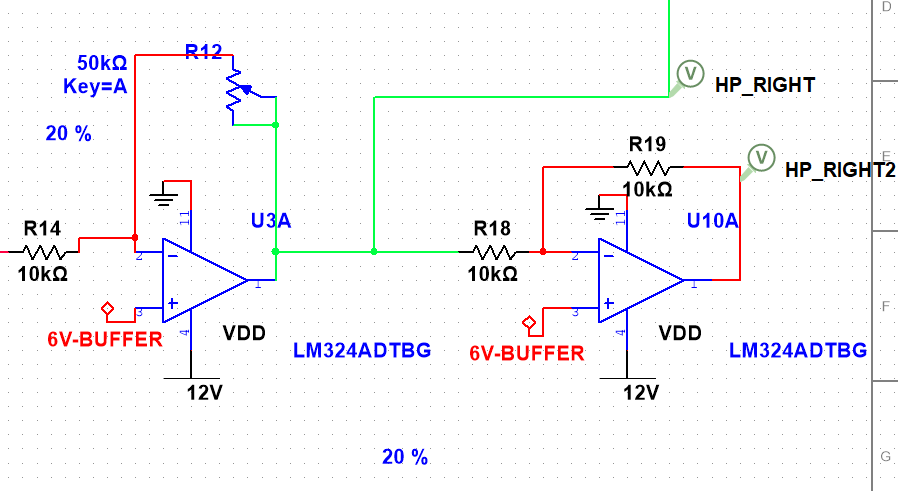
Documentation/Images/Multisim/MultiSim_HP_2.png
