JoeyStrandnes/TSTE93_Slutsteget/Documentation/Images/Multisim/MultiSim_LP.png

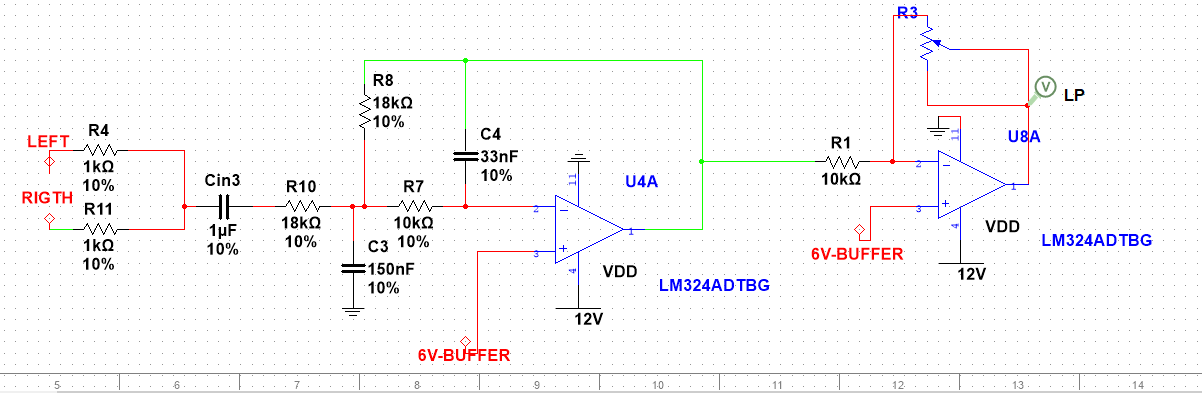
Documentation/Images/Multisim/MultiSim_LP.png
