JoeyStrandnes/TSTE93_Slutsteget/Documentation/Images/Multisim/SE2DIFF.png

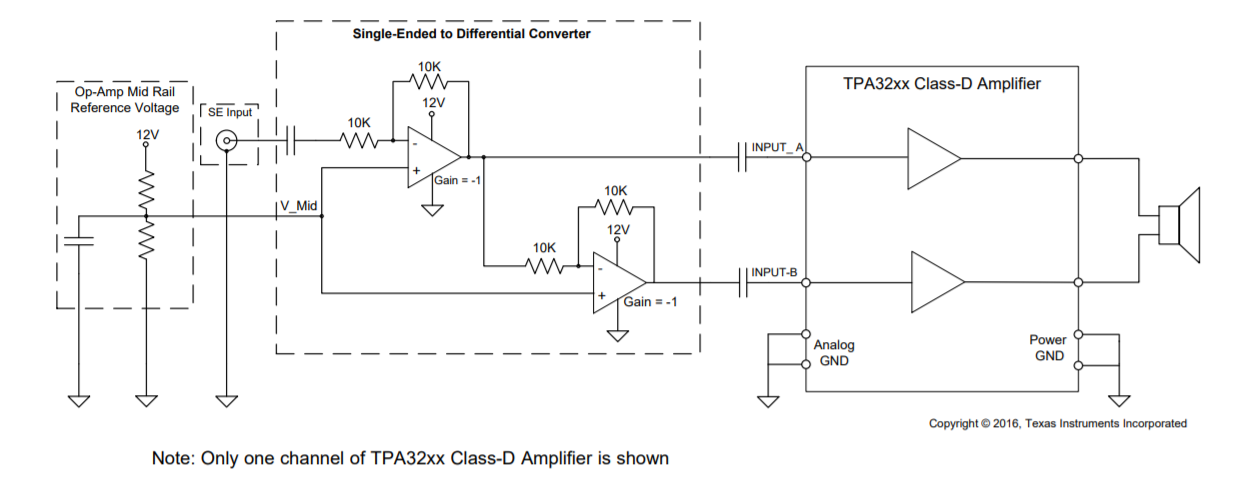
Documentation/Images/Multisim/SE2DIFF.png
