JoeyStrandnes/TSTE93_Slutsteget/Documentation/Images/PSU.jpg

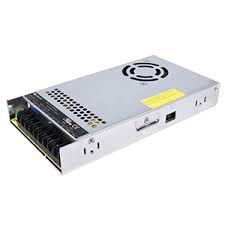
Documentation/Images/PSU.jpg
