JoeyStrandnes/TSTE93_Slutsteget/Documentation/Images/TPA32XX_Master.png

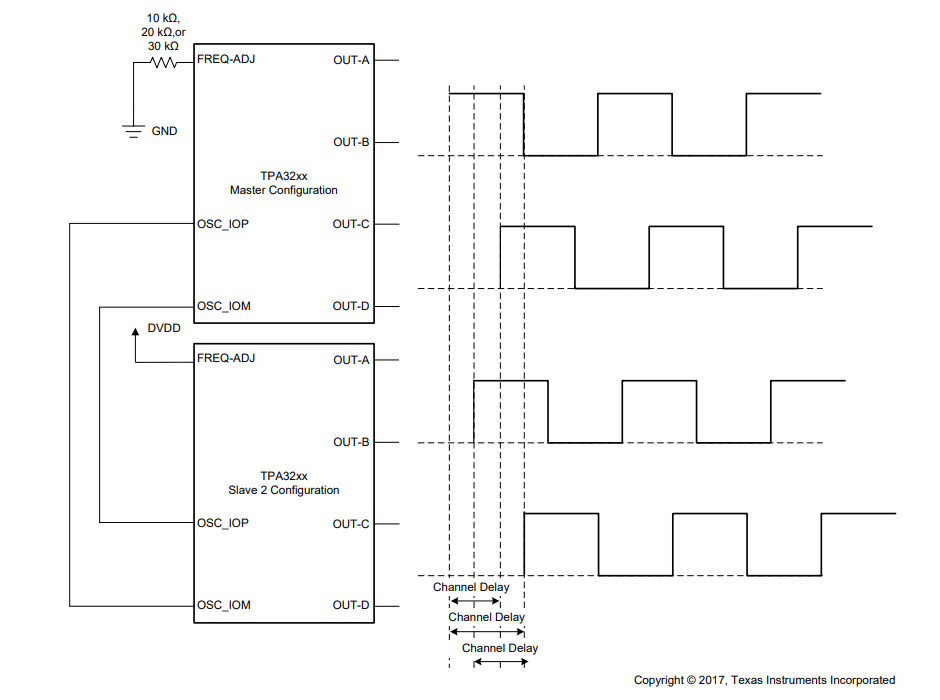
Documentation/Images/TPA32XX_Master.png
