JoeyStrandnes/TSTE93_Slutsteget/Documentation/Images/TPA3244_Power.png

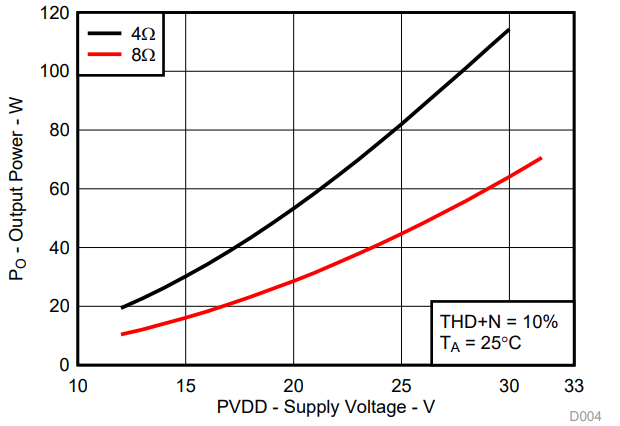
Documentation/Images/TPA3244_Power.png
