JoeyStrandnes/TSTE93_Slutsteget/Documentation/Images/TPA3251_Power.png

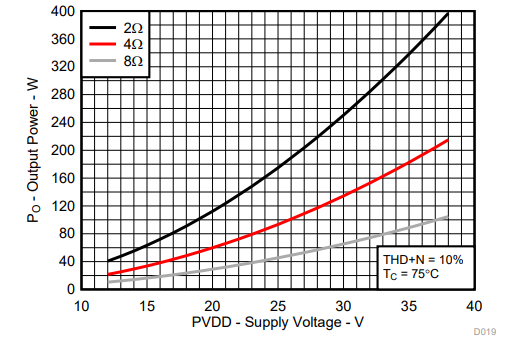
Documentation/Images/TPA3251_Power.png
