JoeyStrandnes/TSTE93_Slutsteget/Documentation/Schematic/Schematic-1.jpg

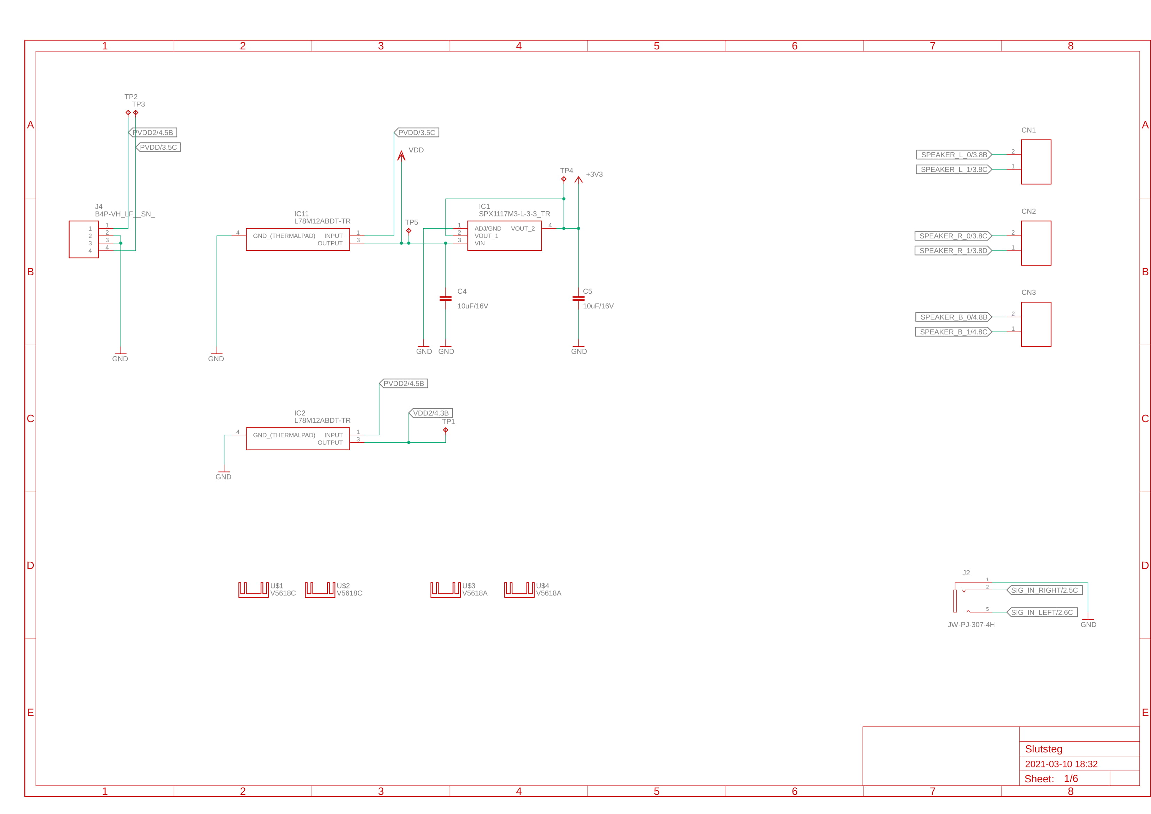
Documentation/Schematic/Schematic-1.jpg
