JoeyStrandnes/TSTE93_Slutsteget/Documentation/Schematic/Schematic-2.jpg

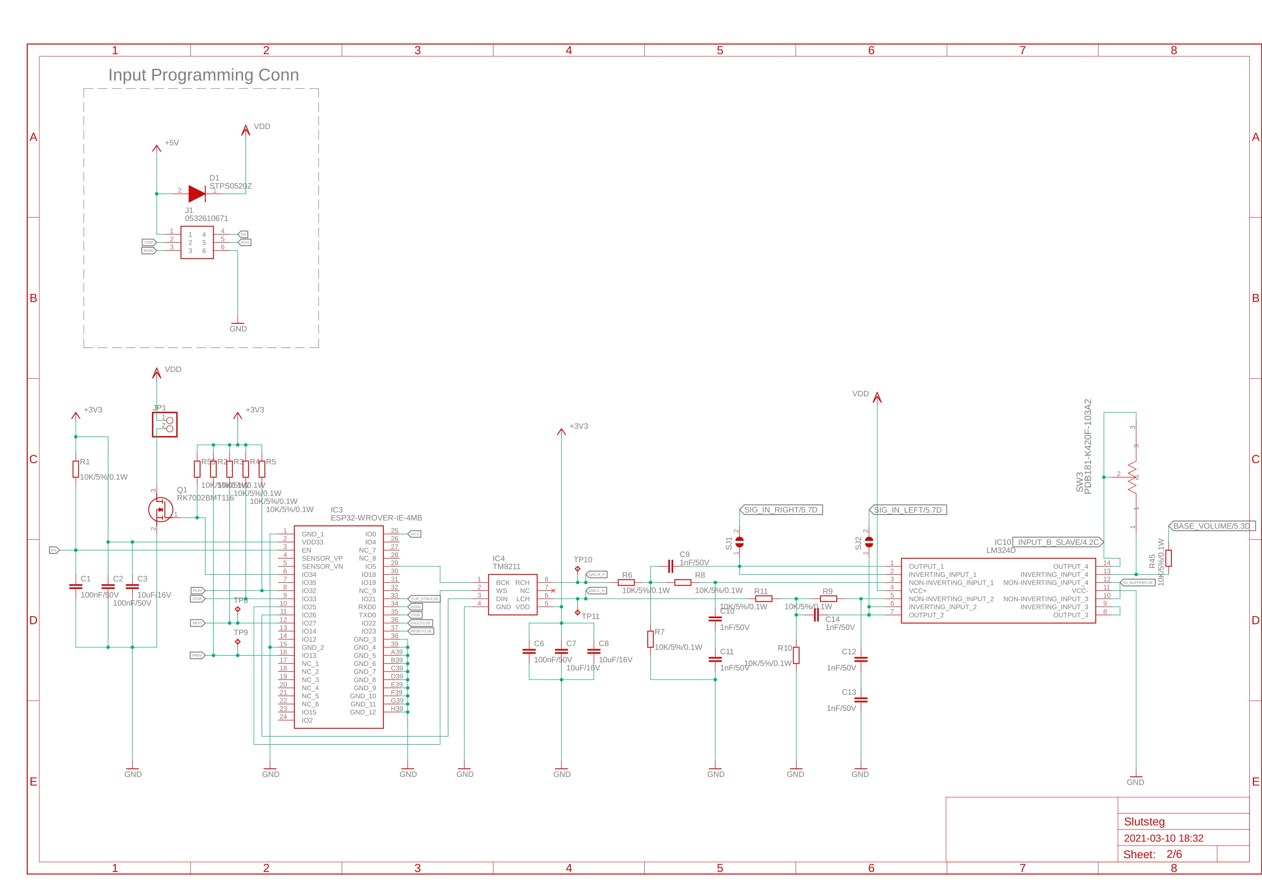
Documentation/Schematic/Schematic-2.jpg
