JoeyStrandnes/TSTE93_Slutsteget/Documentation/Schematic/Schematic-4.jpg

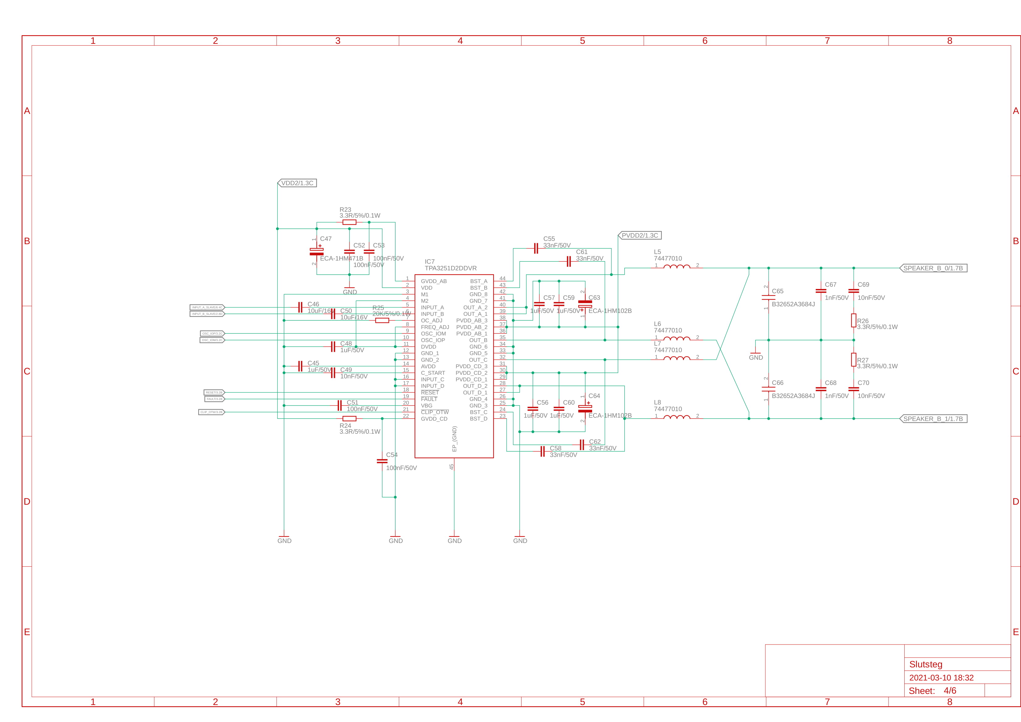
Documentation/Schematic/Schematic-4.jpg
