JoeyStrandnes/TSTE93_Slutsteget/Documentation/Images/Misc/PCB_Above.jpg

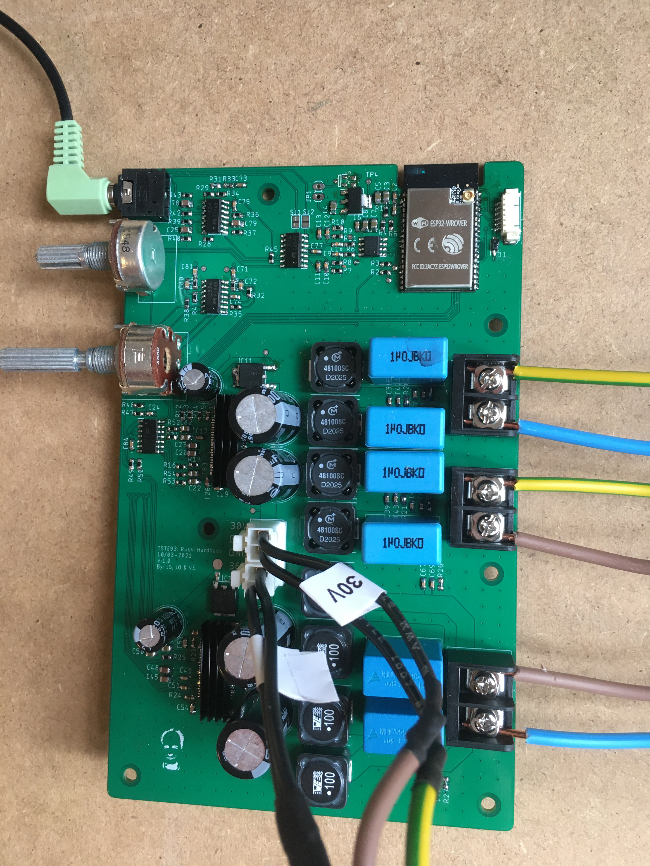
Documentation/Images/Misc/PCB_Above.jpg
